takashicompany/palmslave/images/01.jpg

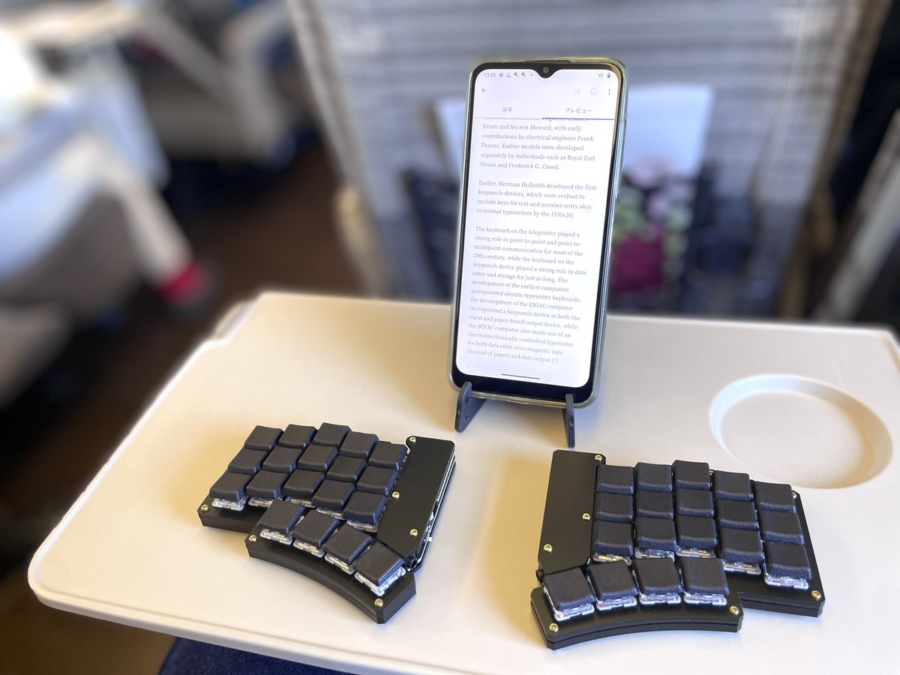
images/01.jpg
