takashicompany/palmslave/images/02.jpg

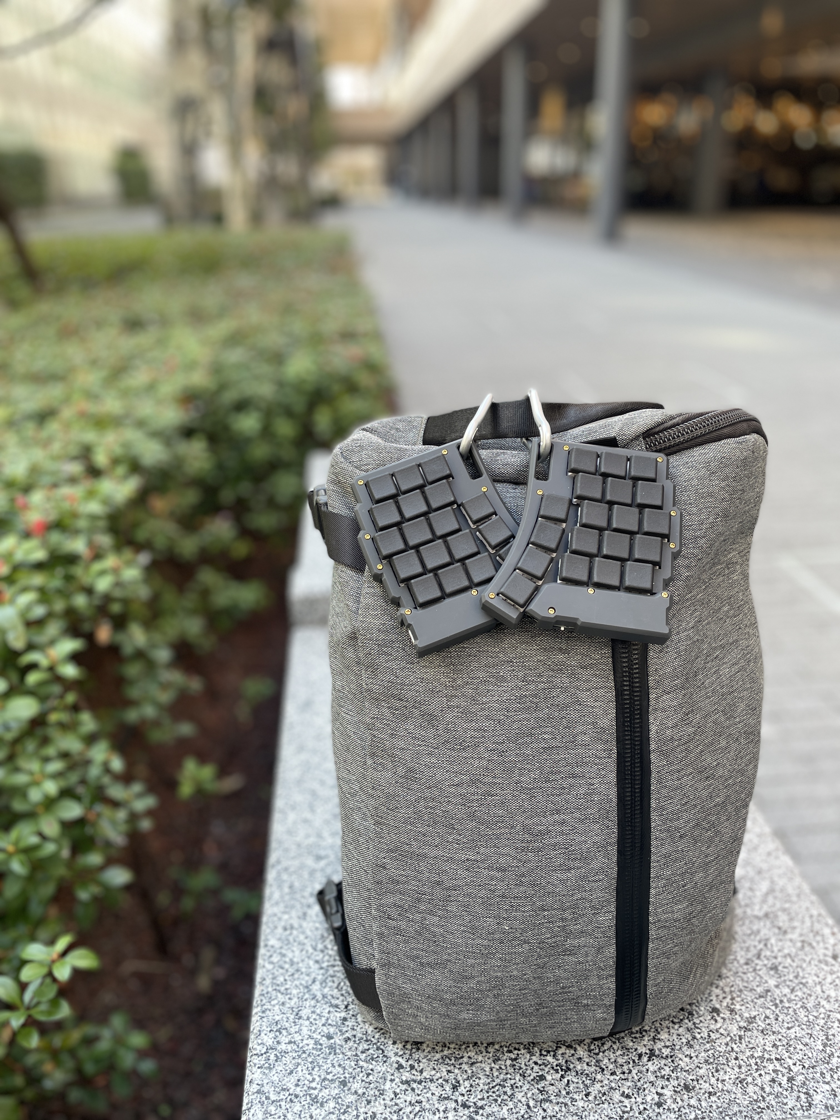
images/02.jpg
