takashicompany/palmslave/images/03.jpg

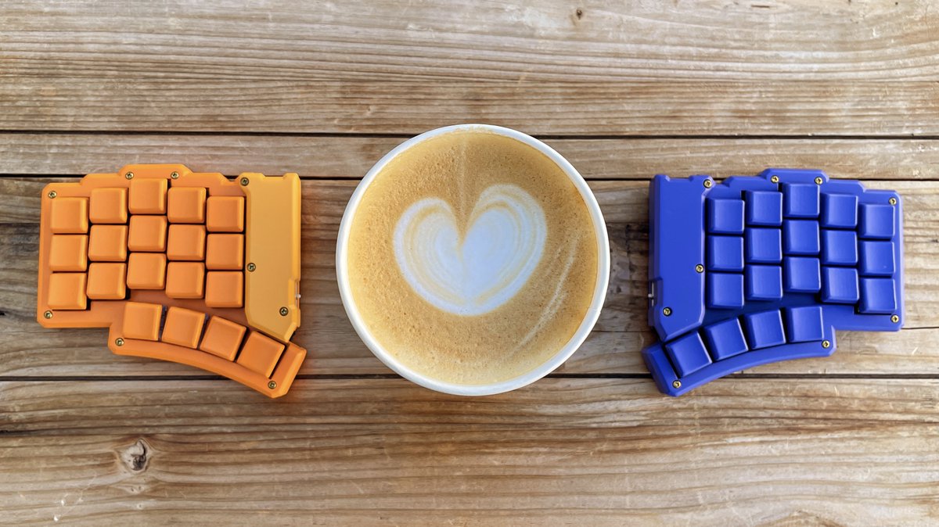
images/03.jpg
