takashicompany/palmslave/images/05.jpg

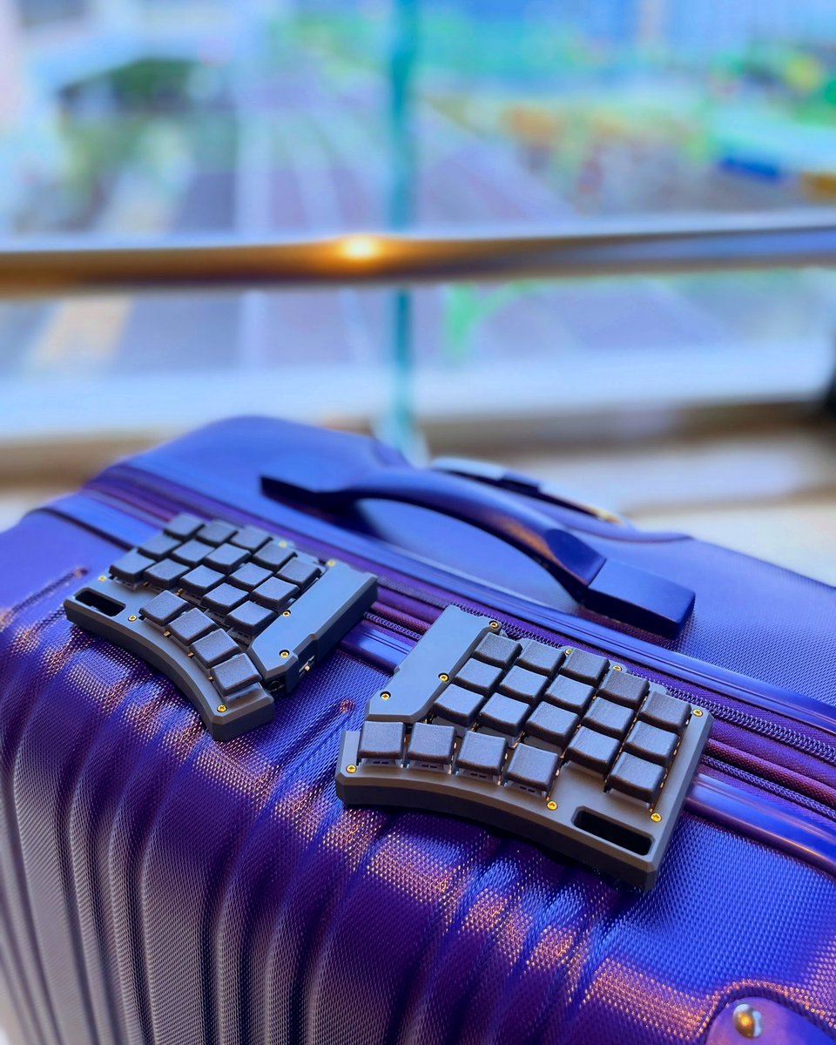
images/05.jpg
