takashicompany/palmslave/images/11.jpg

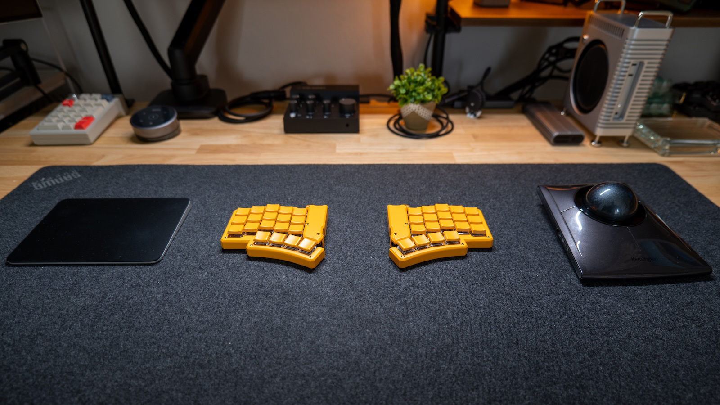
images/11.jpg
