takashicompany/palmslave/images/kawamura/20250201-SDIM0543.jpg

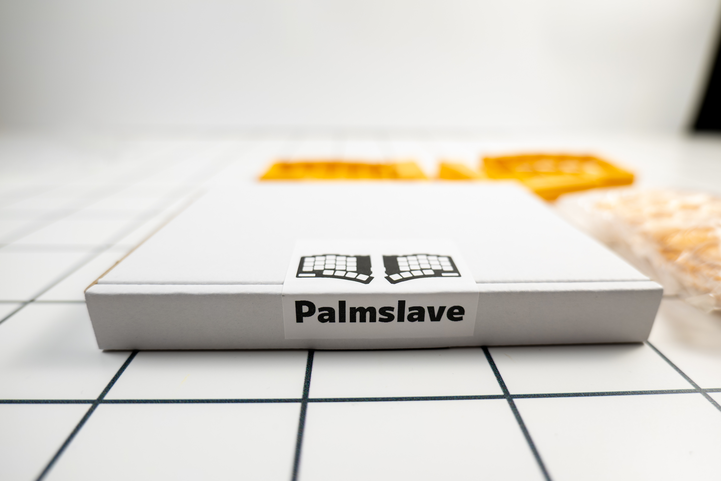
images/kawamura/20250201-SDIM0543.jpg
