takashicompany/palmslave/images/kawamura/20250201-SDIM0548.jpg

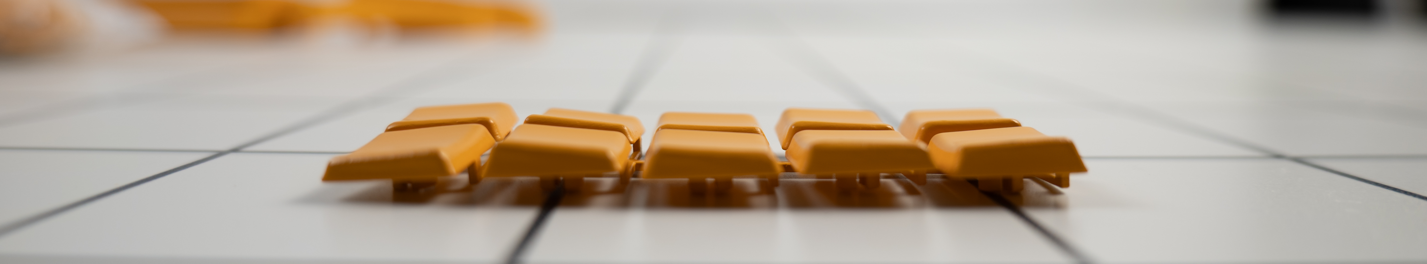
images/kawamura/20250201-SDIM0548.jpg
