takashicompany/palmslave/images/kawamura/20250203-SDIM0584.jpg

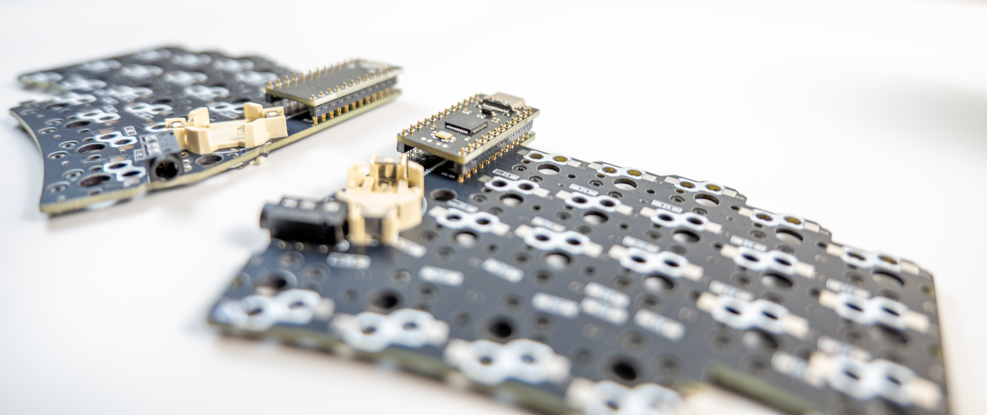
images/kawamura/20250203-SDIM0584.jpg
