takashicompany/palmslave/images/kawamura/20250203-SDIM0585.jpg

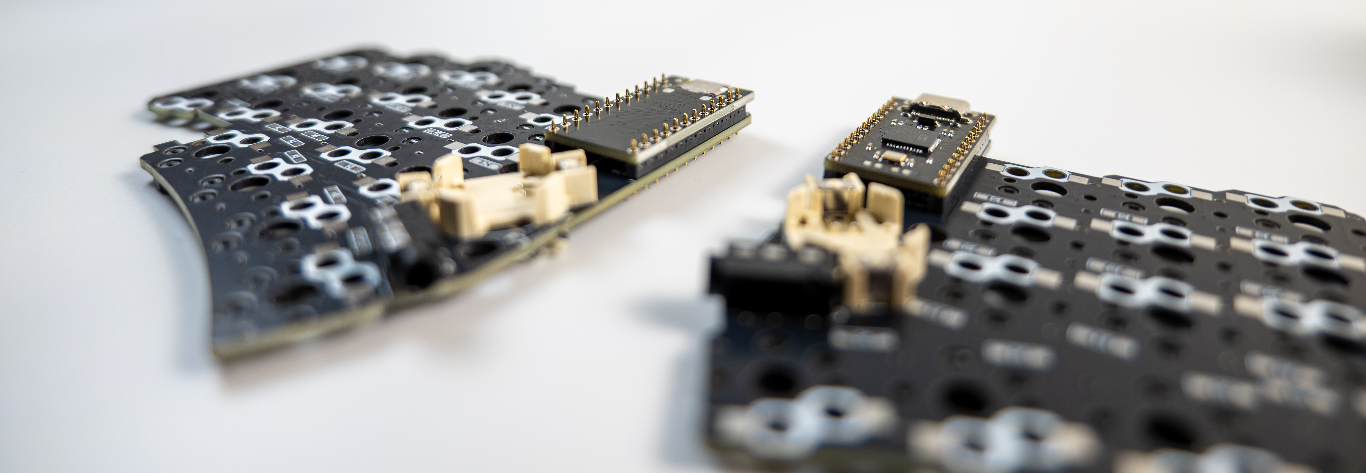
images/kawamura/20250203-SDIM0585.jpg
