takashicompany/palmslave/images/kawamura/20250203-SDIM0596.jpg

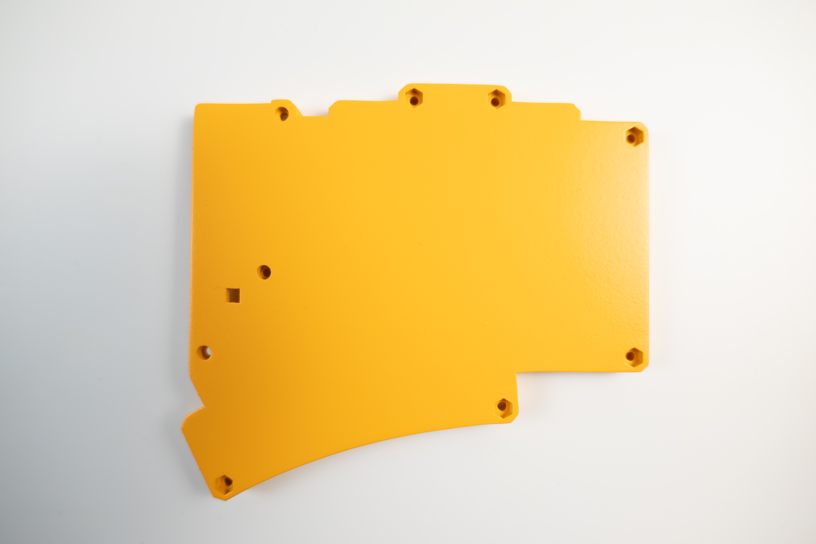
images/kawamura/20250203-SDIM0596.jpg
