takashicompany/palmslave/images/kawamura/20250203-SDIM0607.jpg

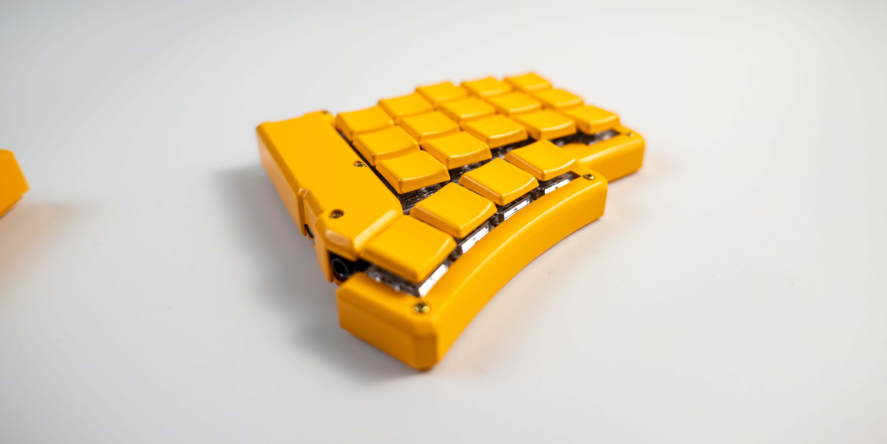
images/kawamura/20250203-SDIM0607.jpg
