takashicompany/palmslave/images/kinotsuyo/palmslave-01.jpg

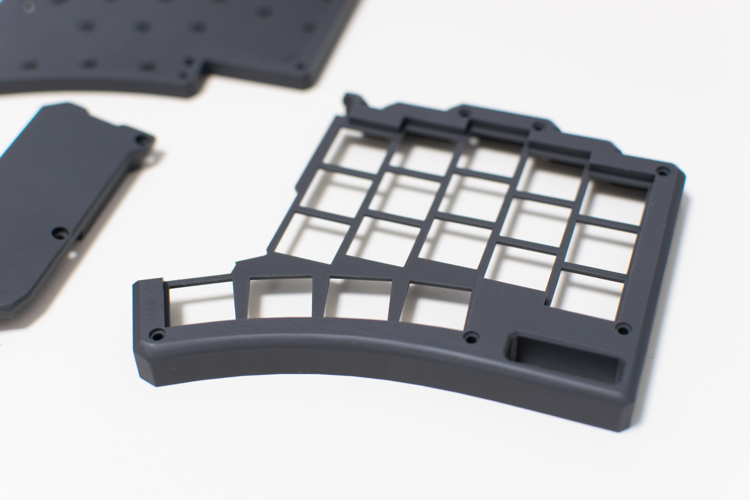
images/kinotsuyo/palmslave-01.jpg
