takashicompany/palmslave/images/kinotsuyo/palmslave-02.jpg

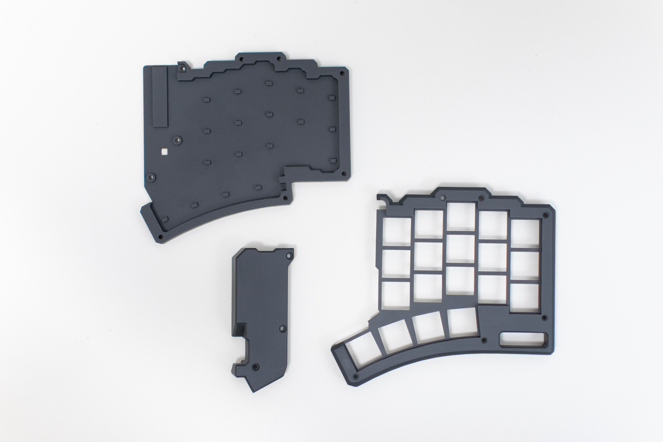
images/kinotsuyo/palmslave-02.jpg
