takashicompany/palmslave/images/kinotsuyo/palmslave-03.jpg

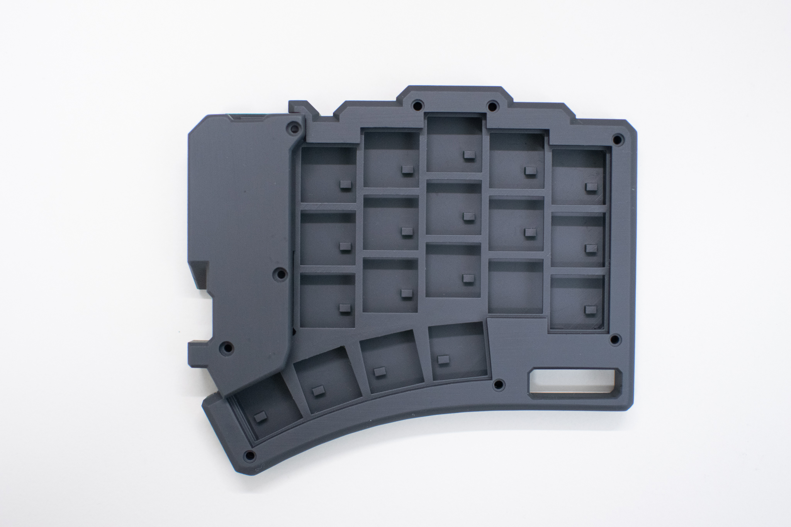
images/kinotsuyo/palmslave-03.jpg
