takashicompany/palmslave/images/kinotsuyo/palmslave-04.jpg

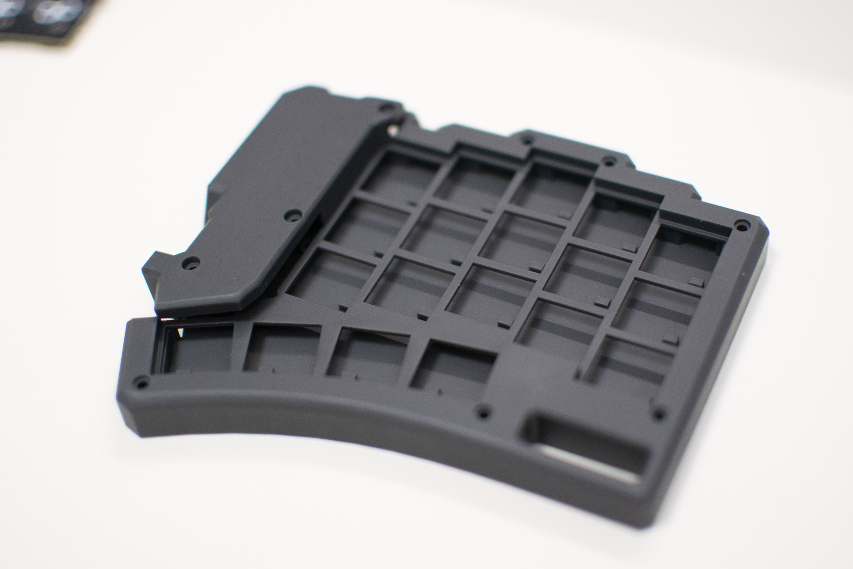
images/kinotsuyo/palmslave-04.jpg
