takashicompany/palmslave/images/kinotsuyo/palmslave-05.jpg

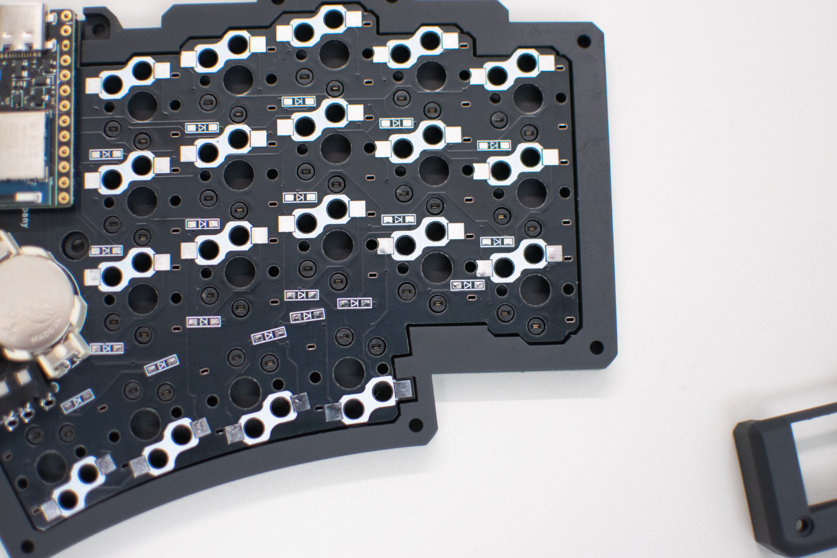
images/kinotsuyo/palmslave-05.jpg
