takashicompany/palmslave/images/kinotsuyo/palmslave-06.jpg

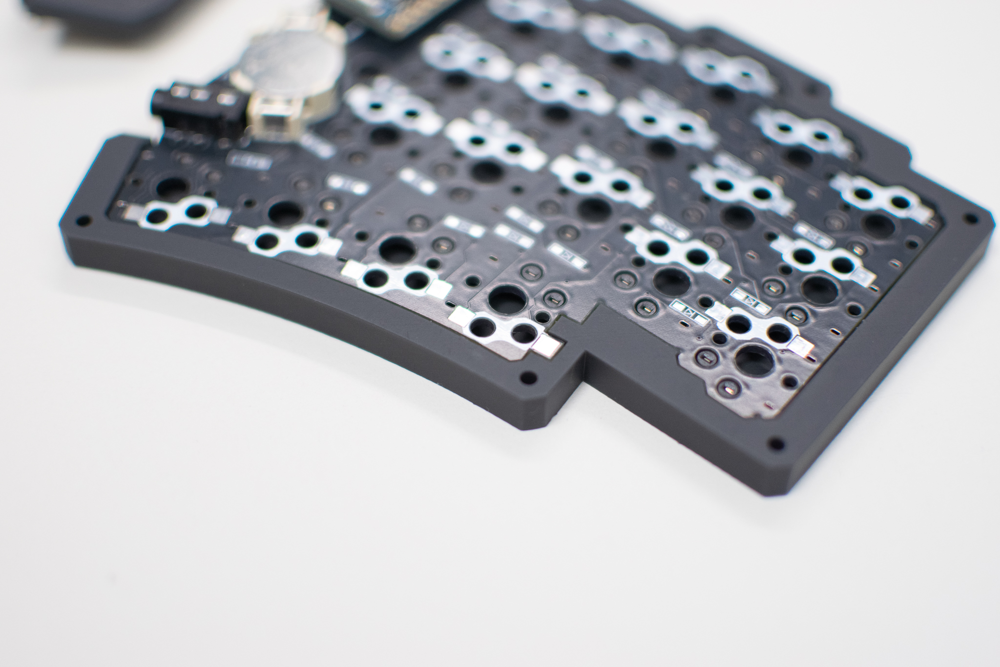
images/kinotsuyo/palmslave-06.jpg
