takashicompany/palmslave/images/kinotsuyo/palmslave-07.jpg

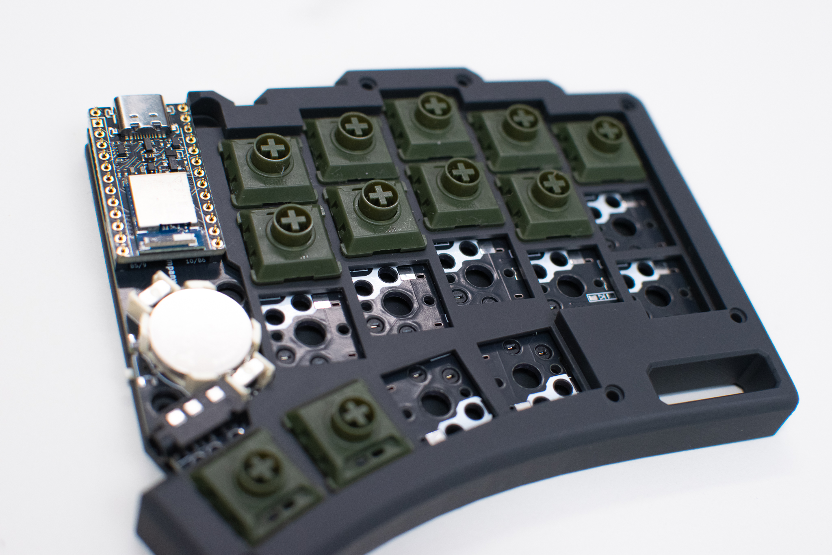
images/kinotsuyo/palmslave-07.jpg
