takashicompany/palmslave/images/kinotsuyo/palmslave-08.jpg

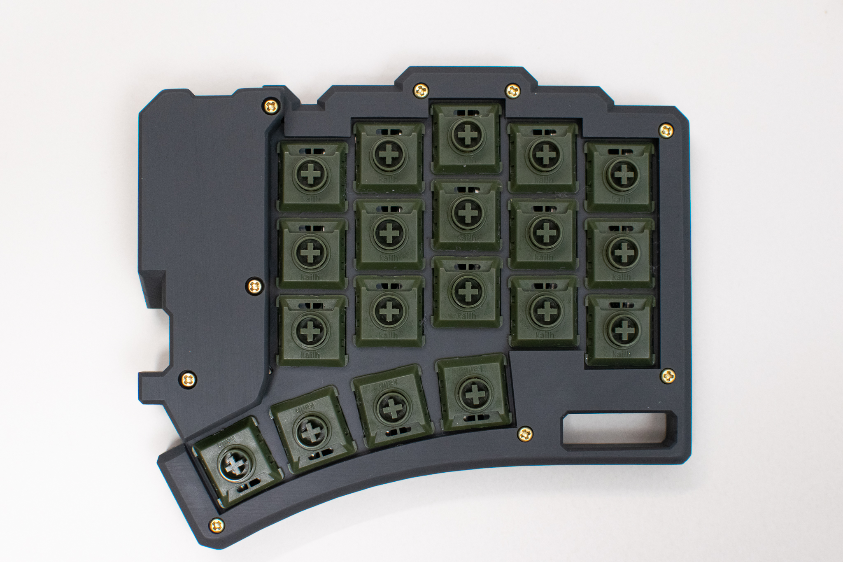
images/kinotsuyo/palmslave-08.jpg
