takashicompany/palmslave/images/kinotsuyo/palmslave-09.jpg

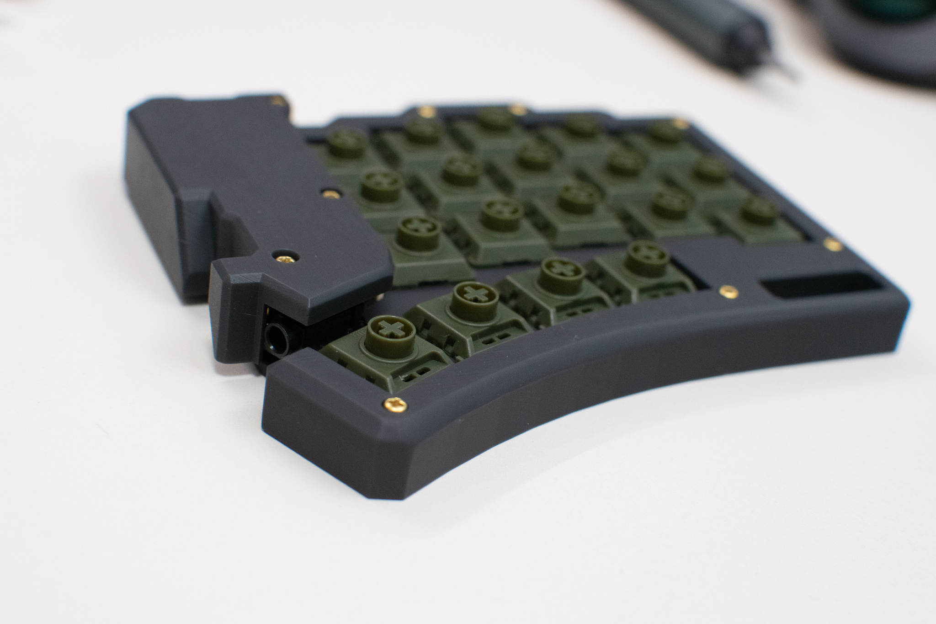
images/kinotsuyo/palmslave-09.jpg
