takashicompany/palmslave/images/kinotsuyo/palmslave-10.jpg

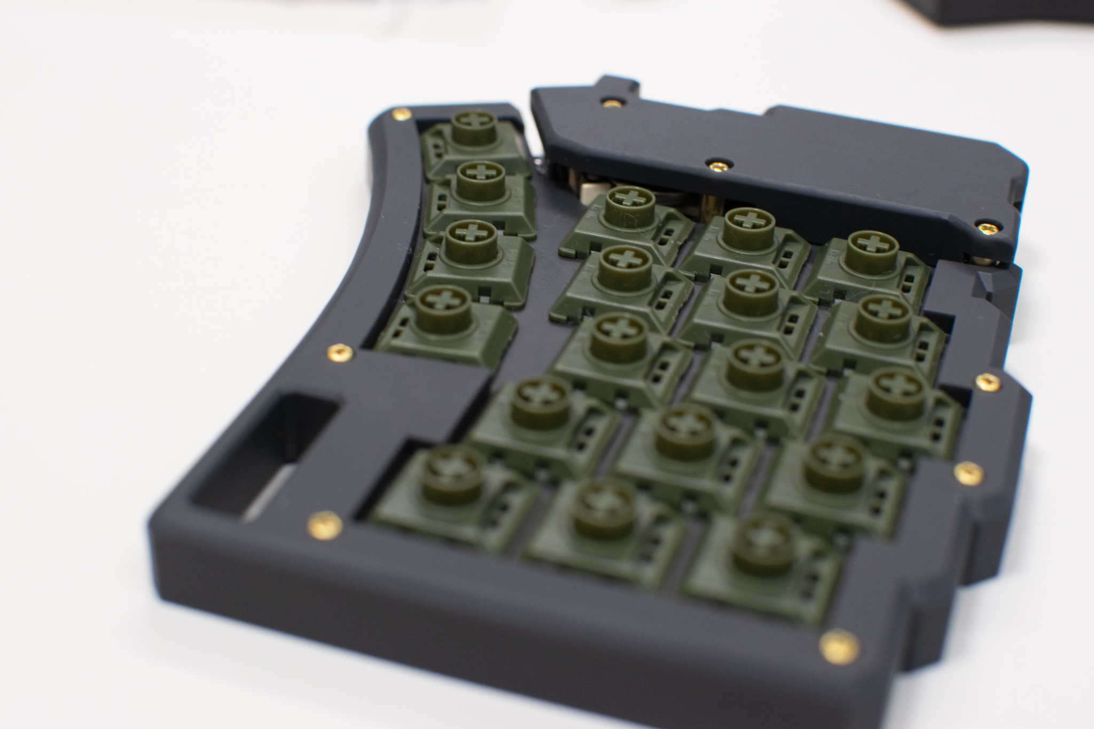
images/kinotsuyo/palmslave-10.jpg
