takashicompany/palmslave/images/kinotsuyo/palmslave-11.jpg

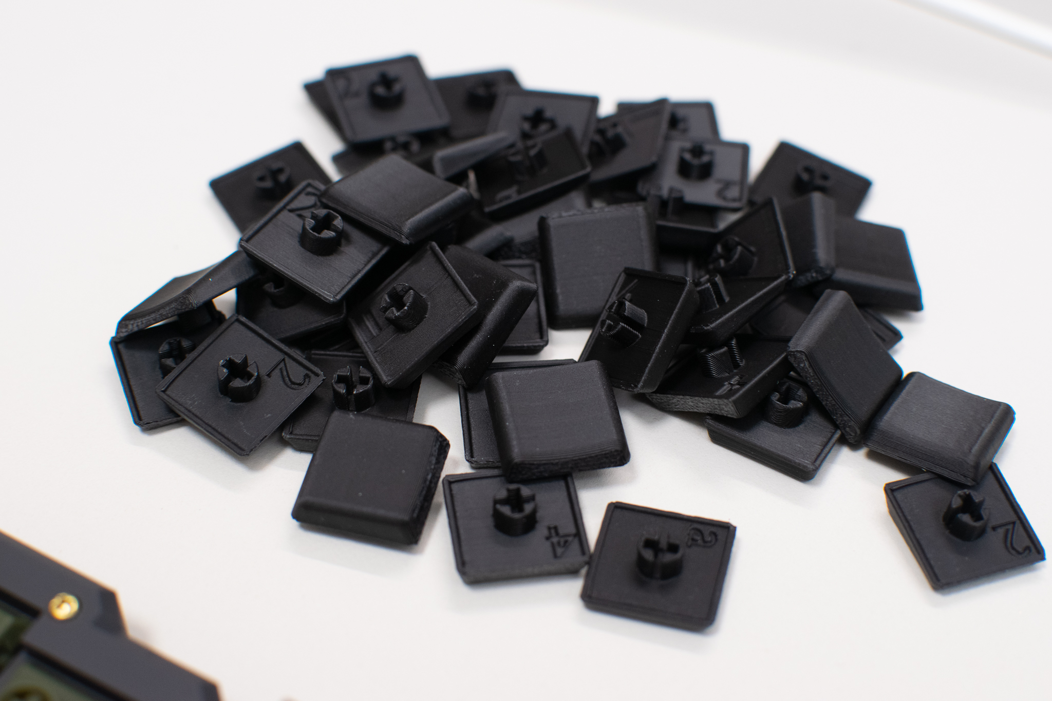
images/kinotsuyo/palmslave-11.jpg
