takashicompany/palmslave/images/kinotsuyo/palmslave-12.jpg

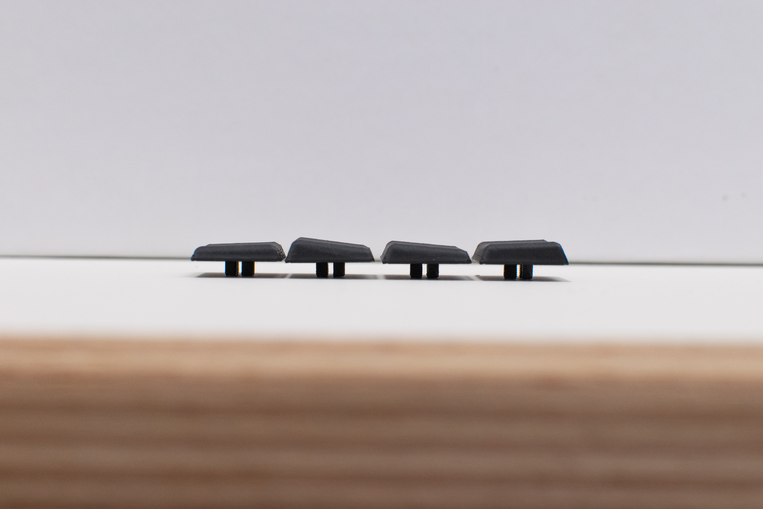
images/kinotsuyo/palmslave-12.jpg
