takashicompany/palmslave/images/kinotsuyo/palmslave-13.jpg

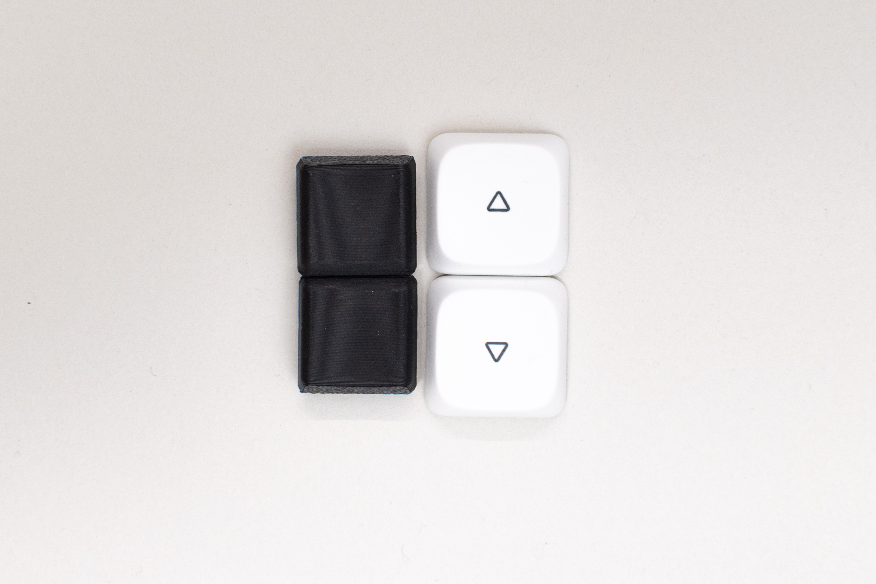
images/kinotsuyo/palmslave-13.jpg
