takashicompany/palmslave/images/kinotsuyo/palmslave-14.jpg

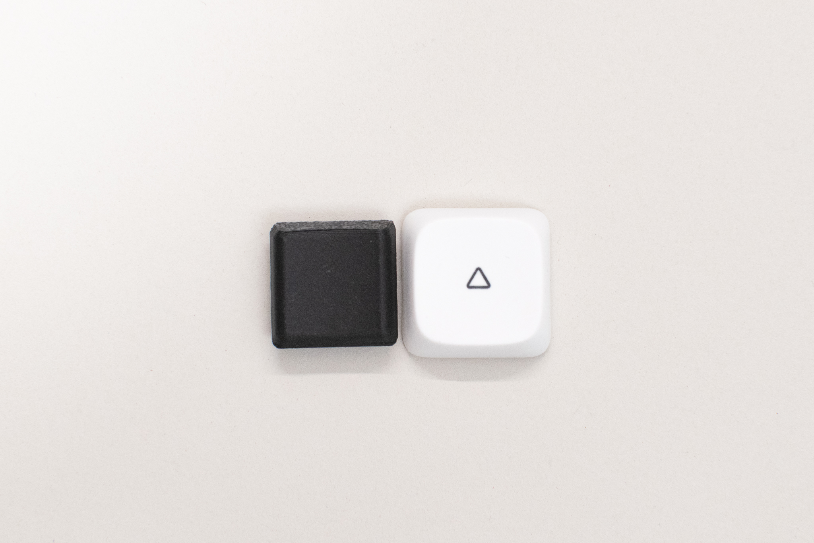
images/kinotsuyo/palmslave-14.jpg
