takashicompany/palmslave/images/kinotsuyo/palmslave-15.jpg

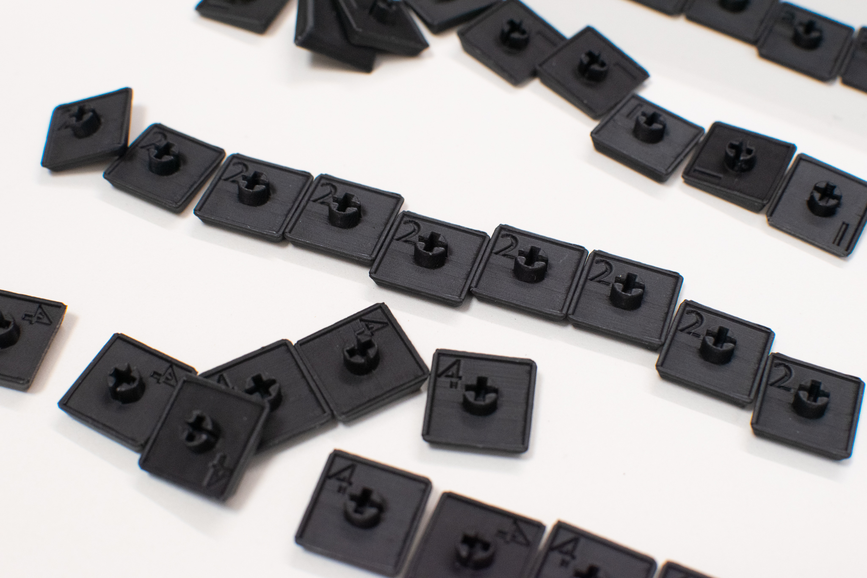
images/kinotsuyo/palmslave-15.jpg
