takashicompany/palmslave/images/kinotsuyo/palmslave-16.jpg

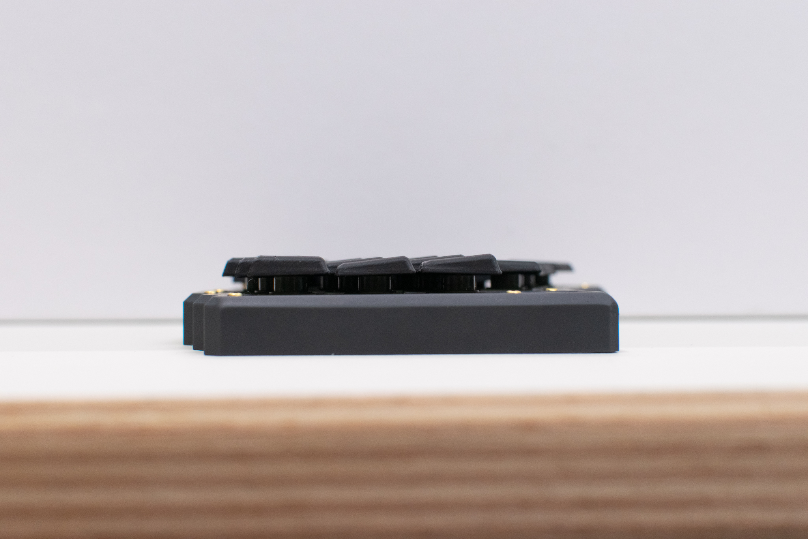
images/kinotsuyo/palmslave-16.jpg
