takashicompany/palmslave/images/kinotsuyo/palmslave-17.jpg

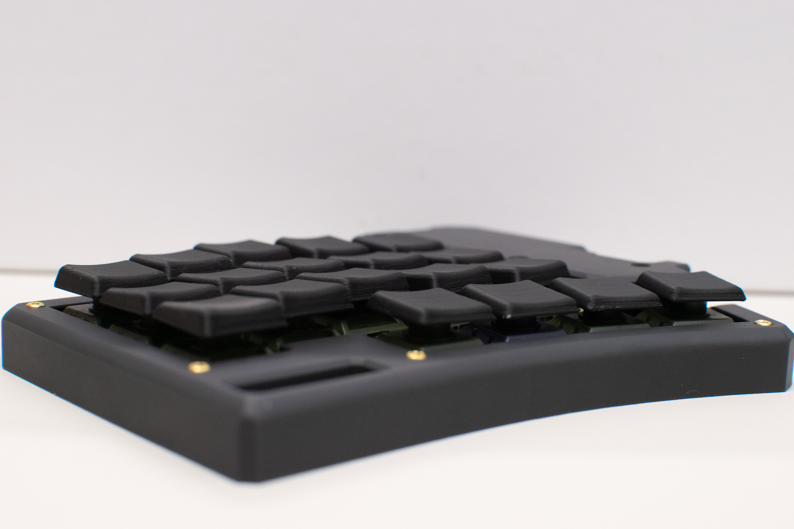
images/kinotsuyo/palmslave-17.jpg
