takashicompany/palmslave/images/kinotsuyo/palmslave-18.jpg

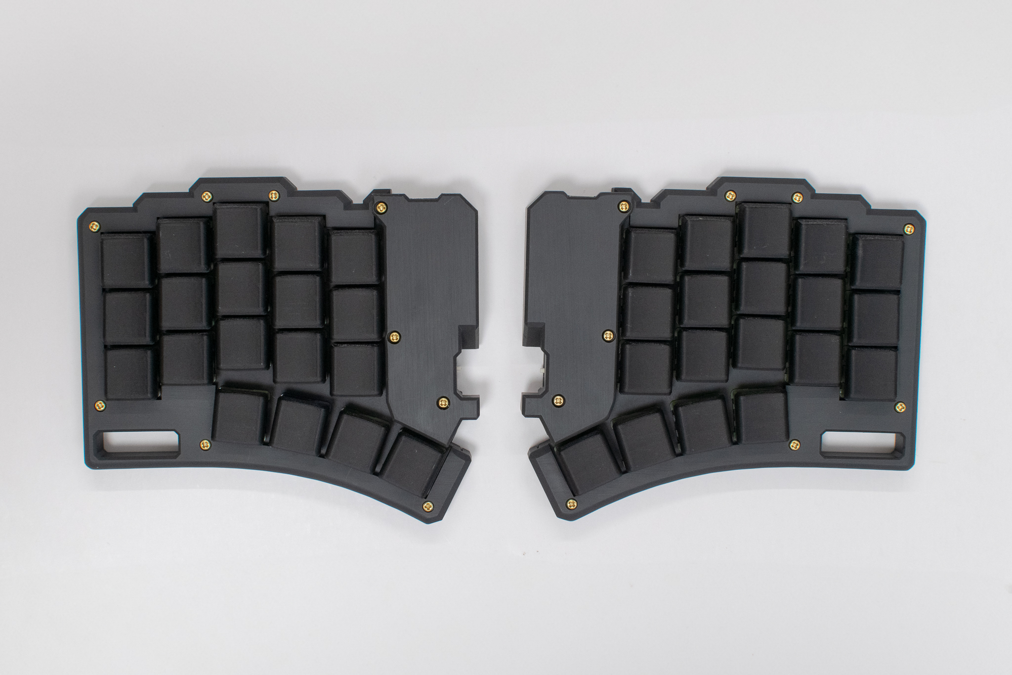
images/kinotsuyo/palmslave-18.jpg
