takashicompany/palmslave/images/kinotsuyo/palmslave-19.jpg

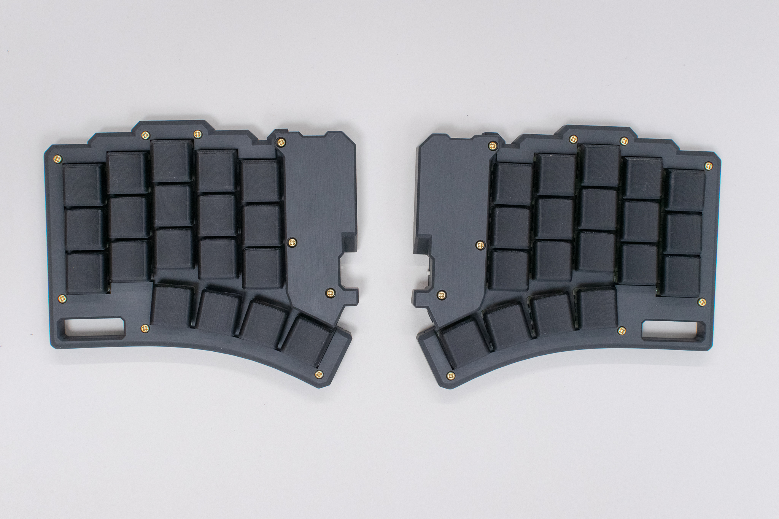
images/kinotsuyo/palmslave-19.jpg
