takashicompany/palmslave/images/kinotsuyo/palmslave-20.jpg

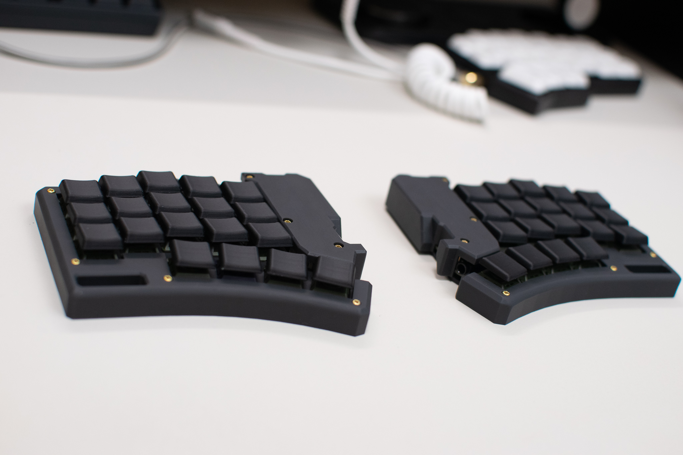
images/kinotsuyo/palmslave-20.jpg
