takashicompany/palmslave/images/kinotsuyo/palmslave-21.jpg

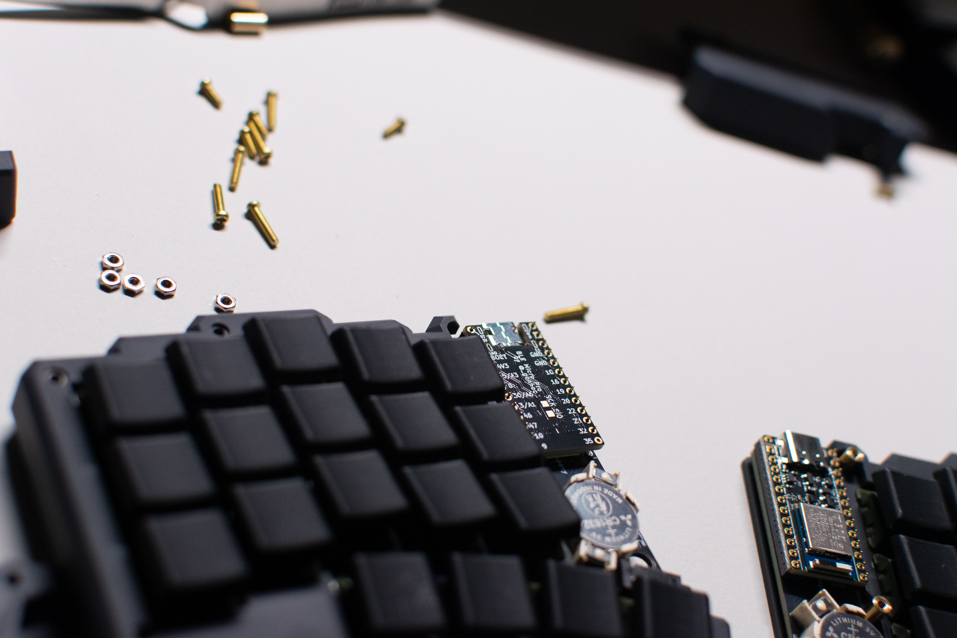
images/kinotsuyo/palmslave-21.jpg
