takashicompany/palmslave/images/kinotsuyo/palmslave-22.jpg

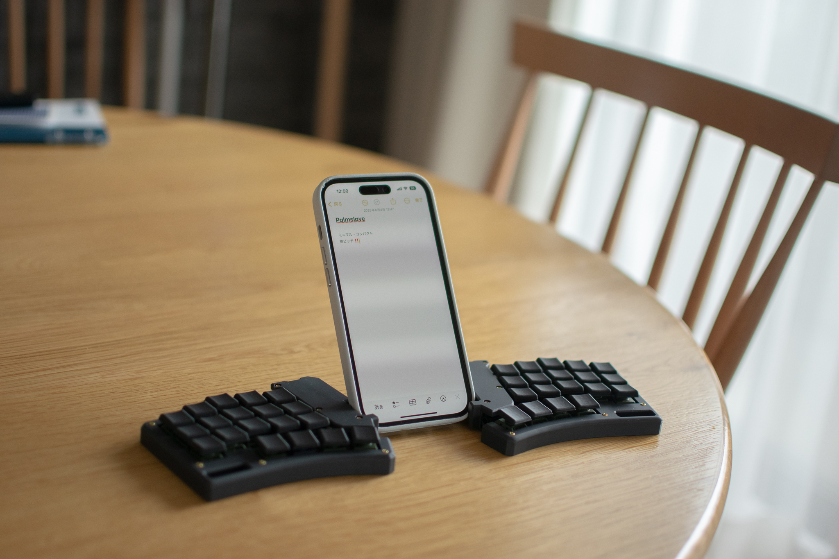
images/kinotsuyo/palmslave-22.jpg
