takashicompany/palmslave/images/kinotsuyo/palmslave-23.jpg

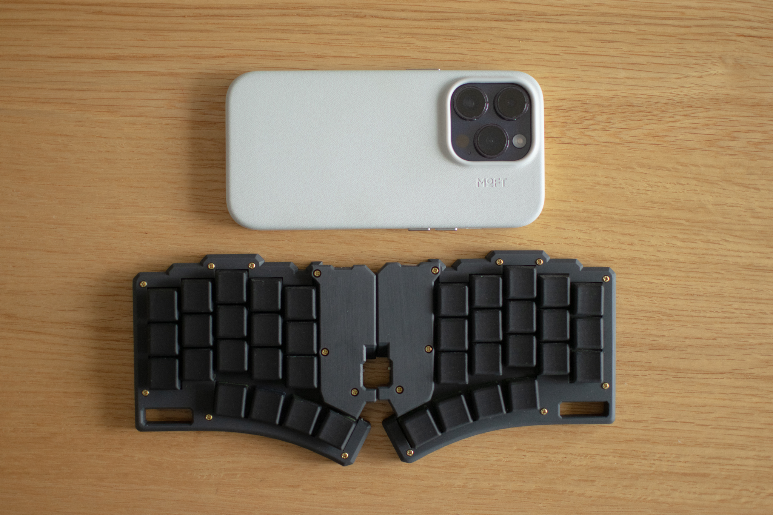
images/kinotsuyo/palmslave-23.jpg
