takashicompany/palmslave/images/kinotsuyo/palmslave-24.jpg

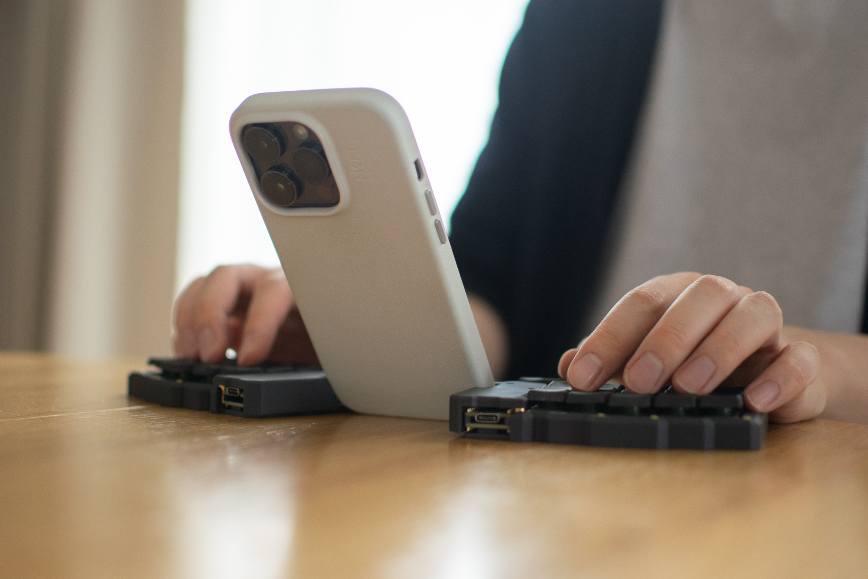
images/kinotsuyo/palmslave-24.jpg
