takashicompany/palmslave/images/kinotsuyo/palmslave-25.jpg

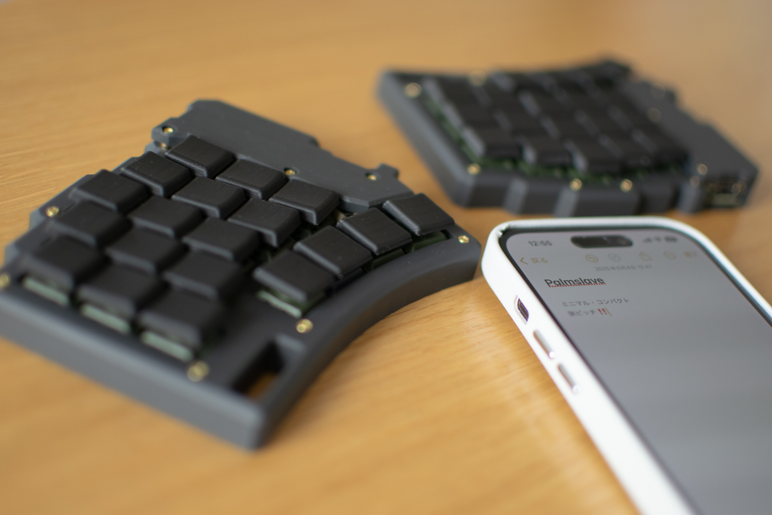
images/kinotsuyo/palmslave-25.jpg
