takashicompany/palmslave/images/kinotsuyo/palmslave-26.jpg

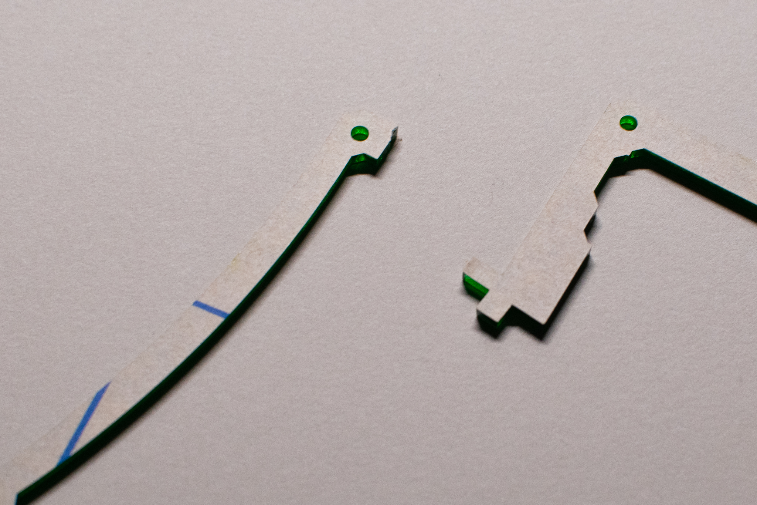
images/kinotsuyo/palmslave-26.jpg
