takashicompany/palmslave/images/kinotsuyo/palmslave-27.jpg

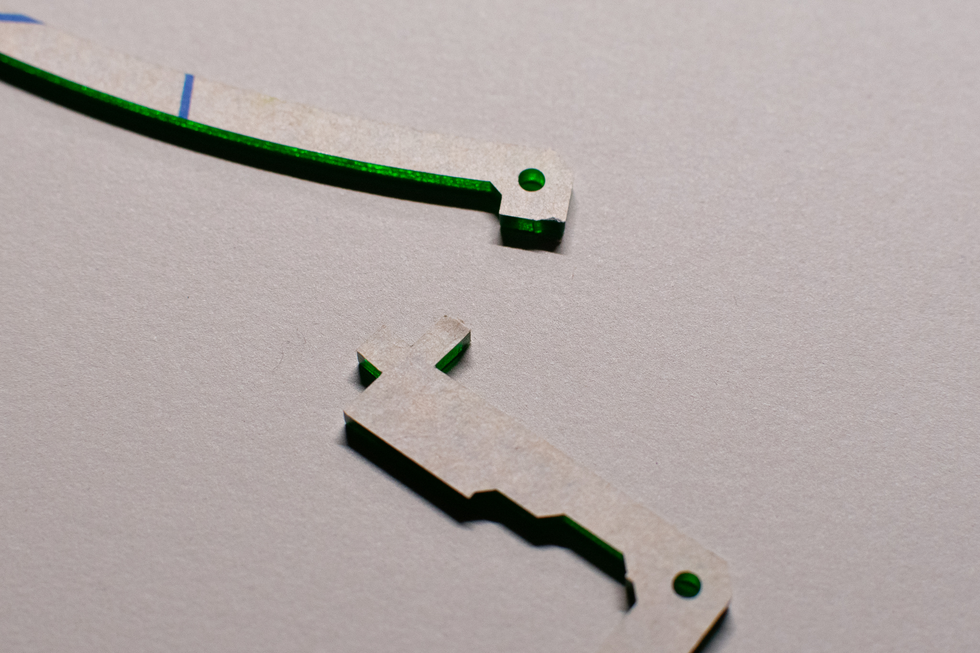
images/kinotsuyo/palmslave-27.jpg
