takashicompany/palmslave/images/kinotsuyo/palmslave-28.jpg

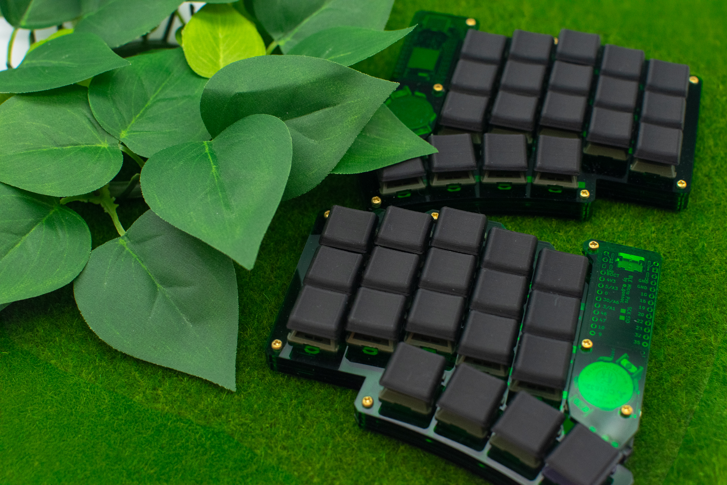
images/kinotsuyo/palmslave-28.jpg
