takashicompany/palmslave/images/kinotsuyo/palmslave-29.jpg

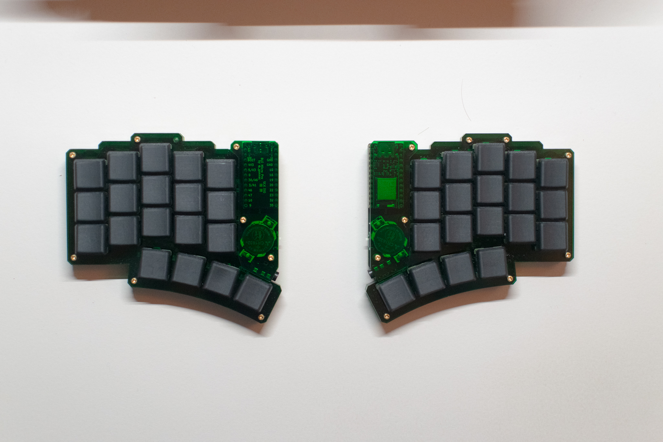
images/kinotsuyo/palmslave-29.jpg
