takashicompany/palmslave/images/kinotsuyo/palmslave-30.jpg

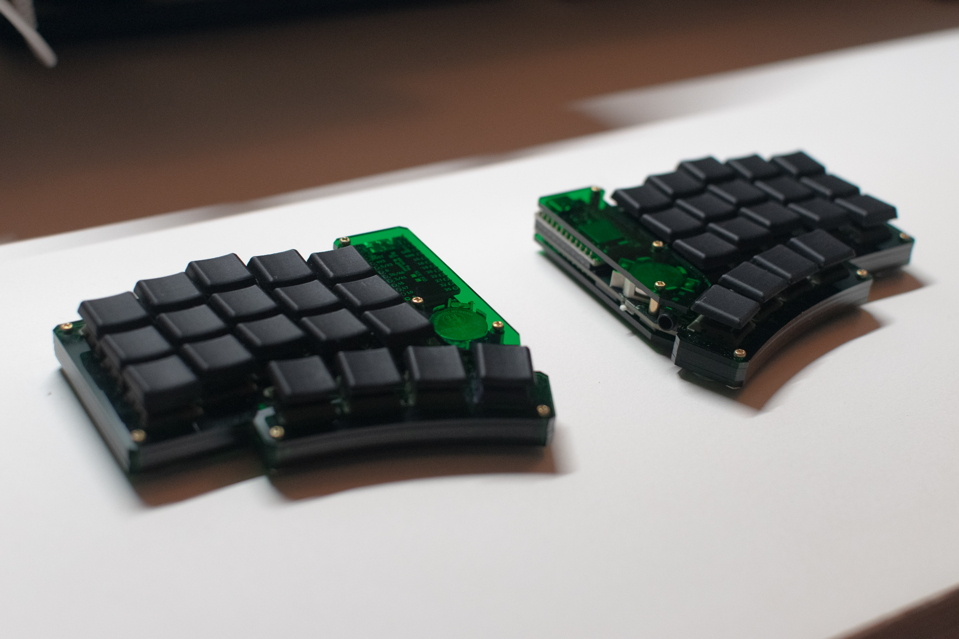
images/kinotsuyo/palmslave-30.jpg
