takashicompany/palmslave/images/kinotsuyo/palmslave-31.jpg

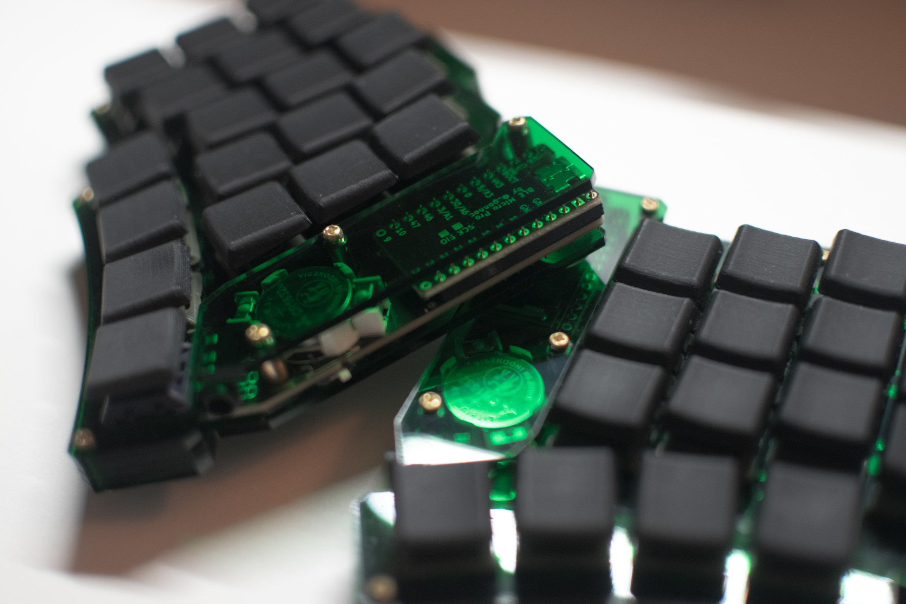
images/kinotsuyo/palmslave-31.jpg
