takashicompany/palmslave/images/kinotsuyo/palmslave-32.jpg

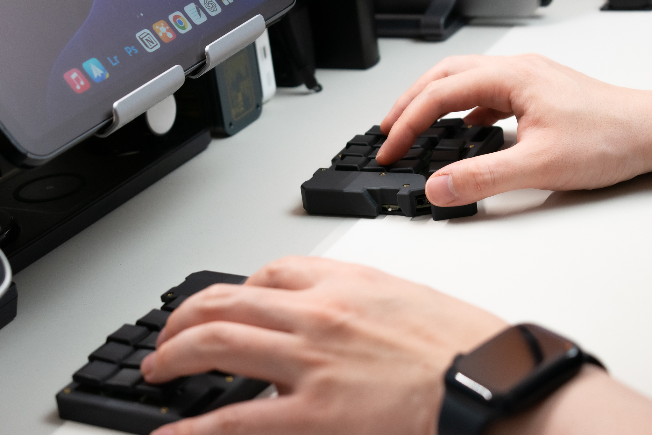
images/kinotsuyo/palmslave-32.jpg
