takashicompany/palmslave/images/kinotsuyo/palmslave-33.jpg

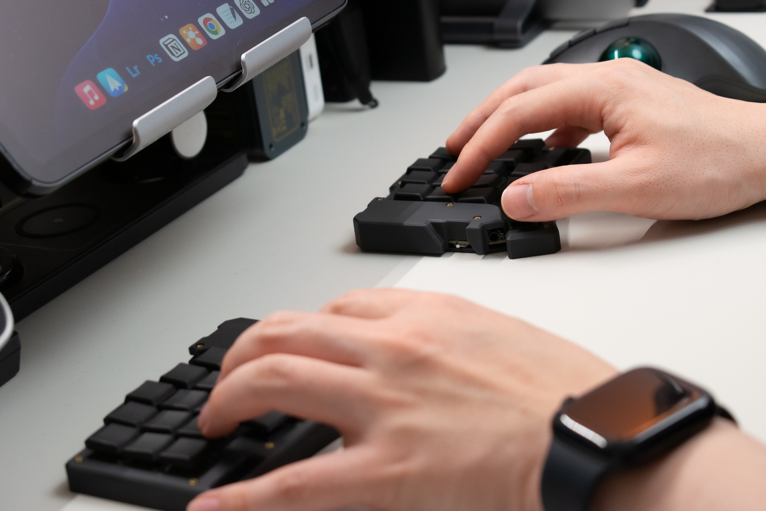
images/kinotsuyo/palmslave-33.jpg
