takashicompany/palmslave/images/kinotsuyo/palmslave-34.jpg

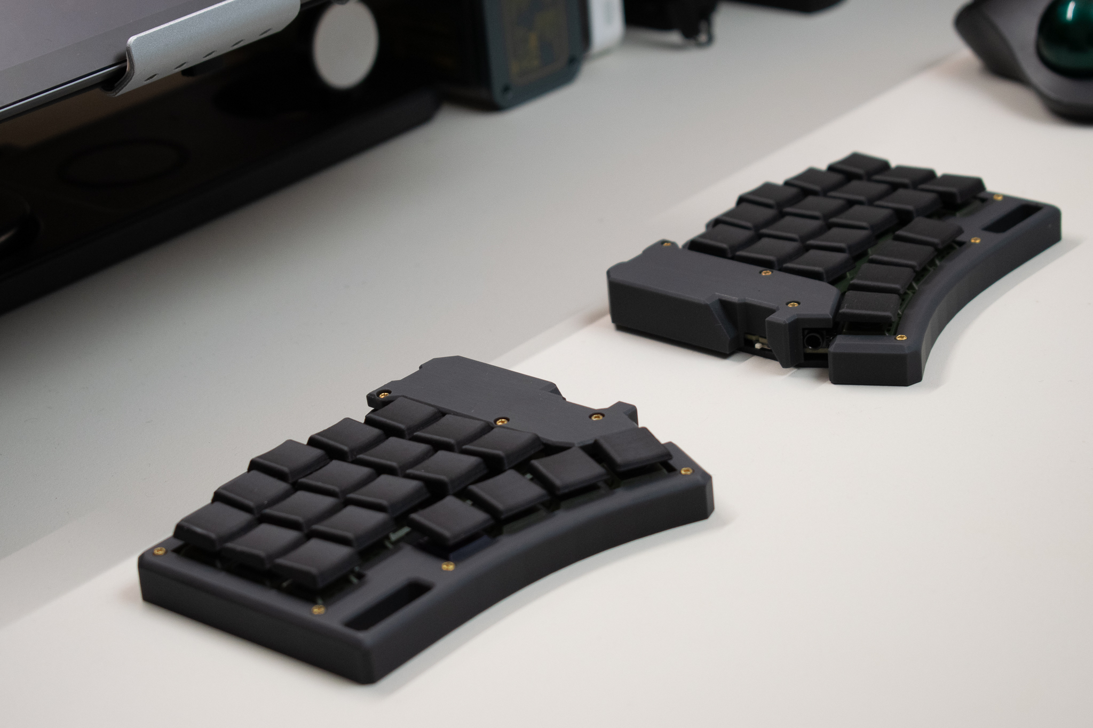
images/kinotsuyo/palmslave-34.jpg
