takashicompany/palmslave/images/kinotsuyo/palmslave-35.jpg

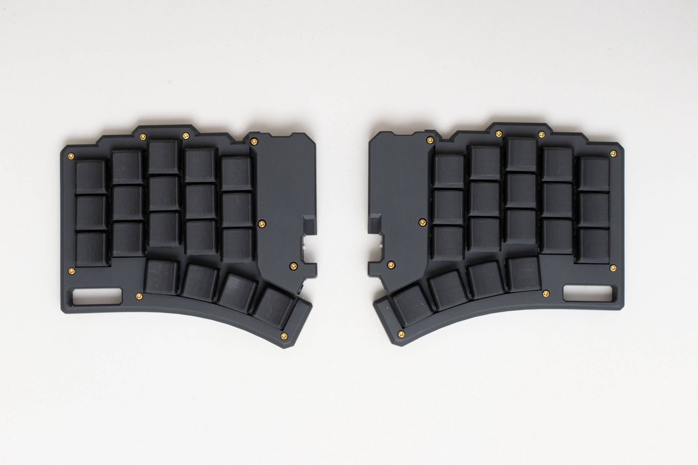
images/kinotsuyo/palmslave-35.jpg
