takashicompany/palmslave/images/kinotsuyo/palmslave-36.jpg

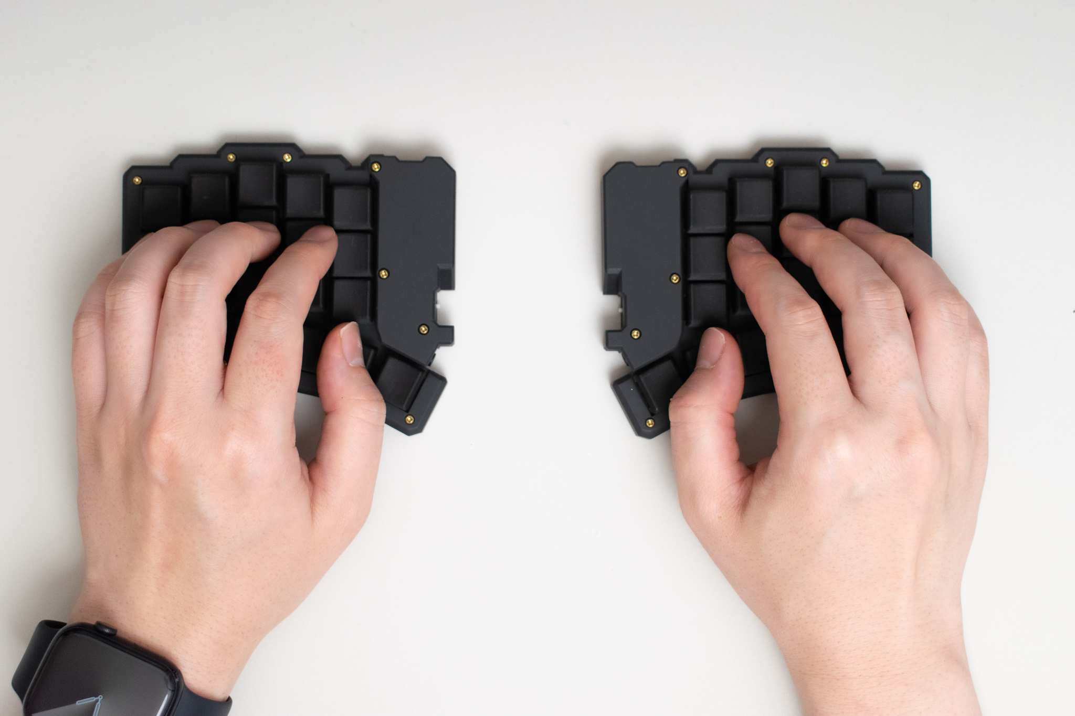
images/kinotsuyo/palmslave-36.jpg
