takashicompany/palmslave/images/kinotsuyo/palmslave-37.jpg

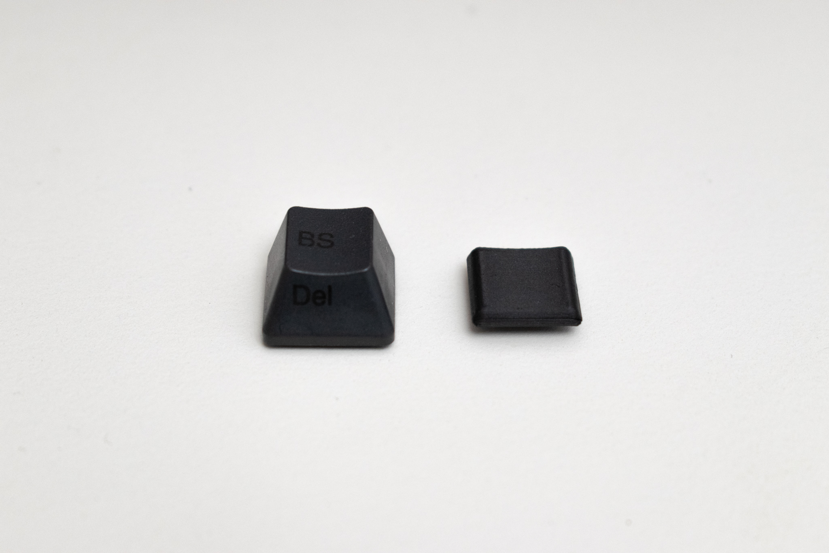
images/kinotsuyo/palmslave-37.jpg
