takashicompany/palmslave/images/kinotsuyo/palmslave-38.jpg

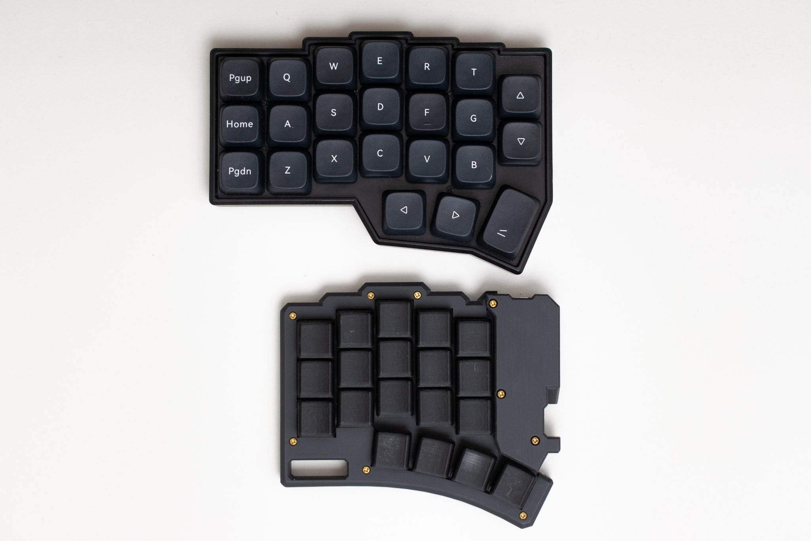
images/kinotsuyo/palmslave-38.jpg
