takashicompany/palmslave/images/kinotsuyo/palmslave-39.jpg

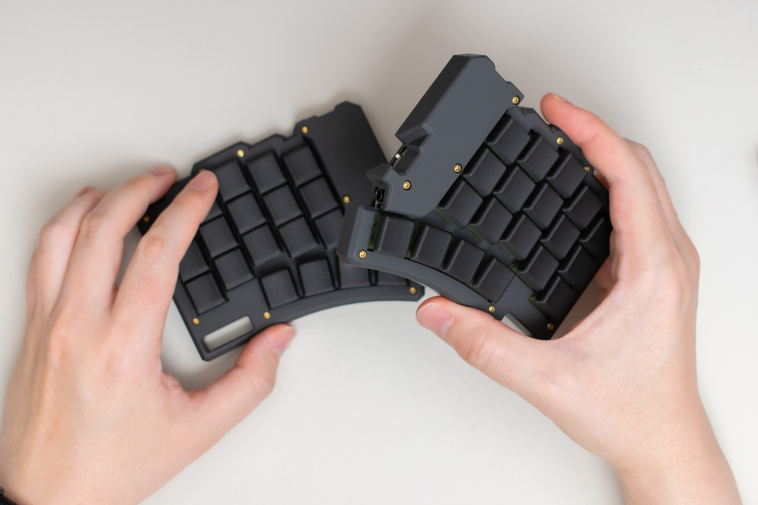
images/kinotsuyo/palmslave-39.jpg
