takashicompany/palmslave/images/kinotsuyo/palmslave-40.jpg

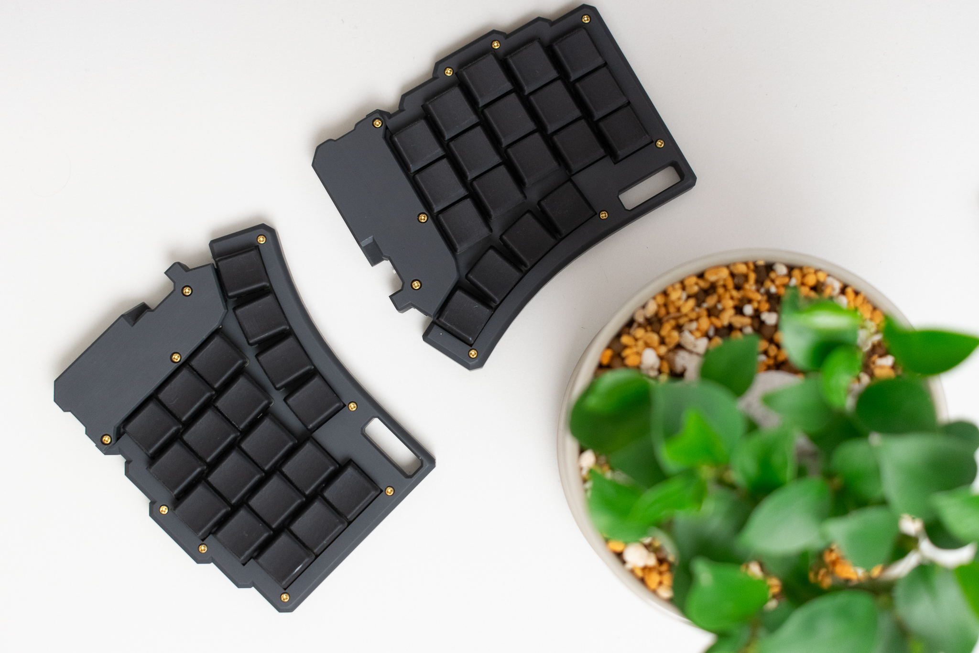
images/kinotsuyo/palmslave-40.jpg
