takashicompany/palmslave/images/kinotsuyo/palmslave-41.jpg

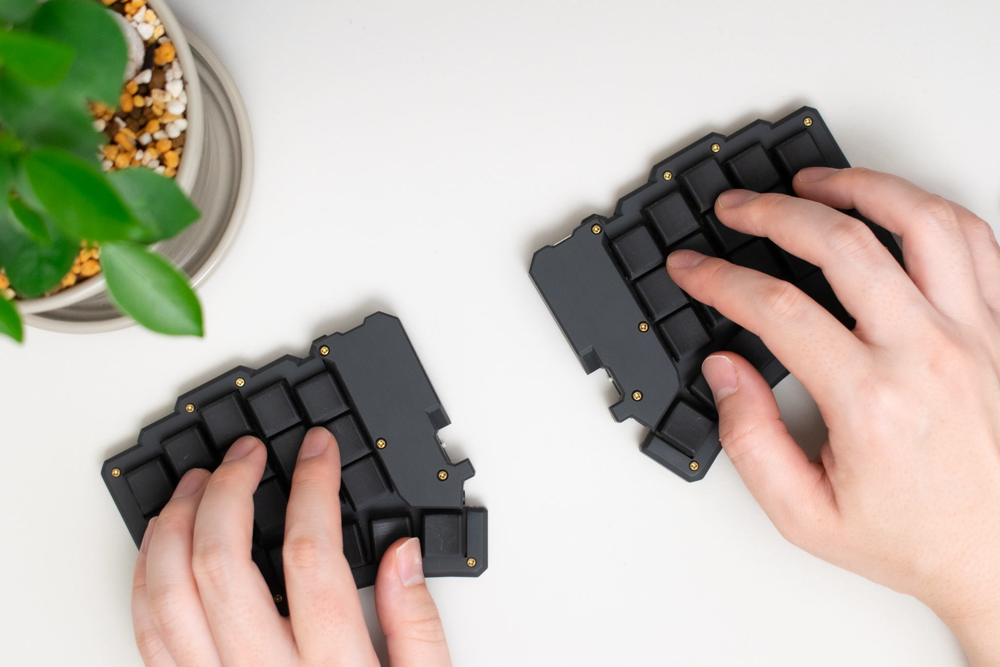
images/kinotsuyo/palmslave-41.jpg
