takashicompany/palmslave/images/kinotsuyo/palmslave-42.jpg

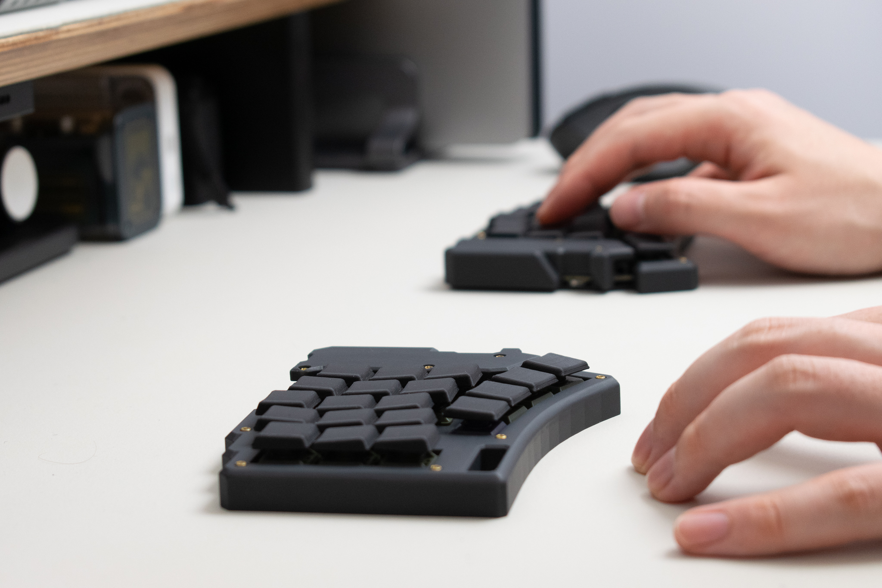
images/kinotsuyo/palmslave-42.jpg
