takashicompany/palmslave/images/kinotsuyo/palmslave-43.jpg

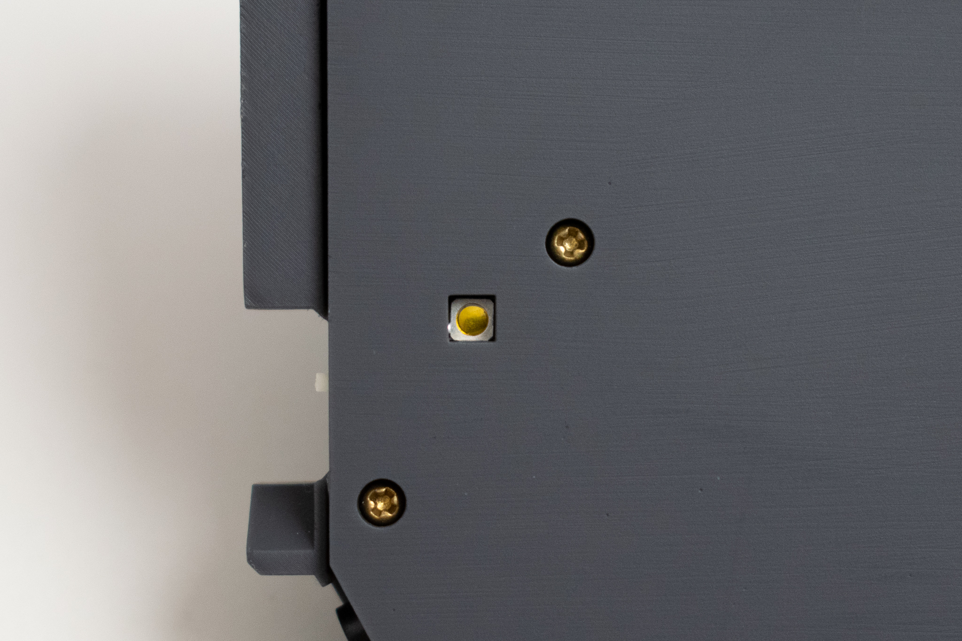
images/kinotsuyo/palmslave-43.jpg
