takashicompany/palmslave/images/kinotsuyo/palmslave-44.jpg

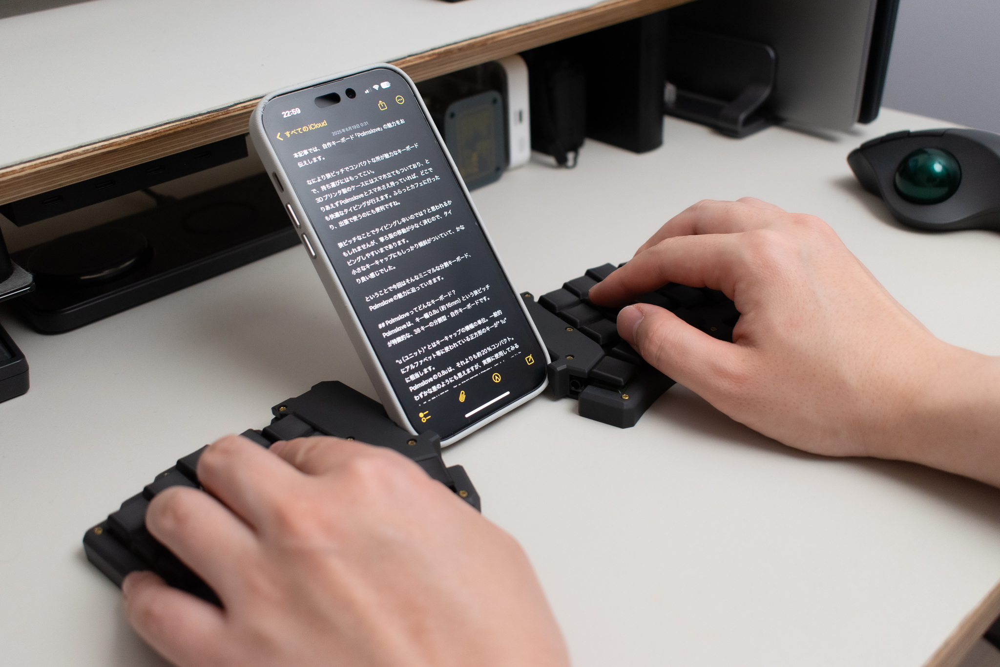
images/kinotsuyo/palmslave-44.jpg
