takashicompany/palmslave/images/kinotsuyo/palmslave-45.jpg

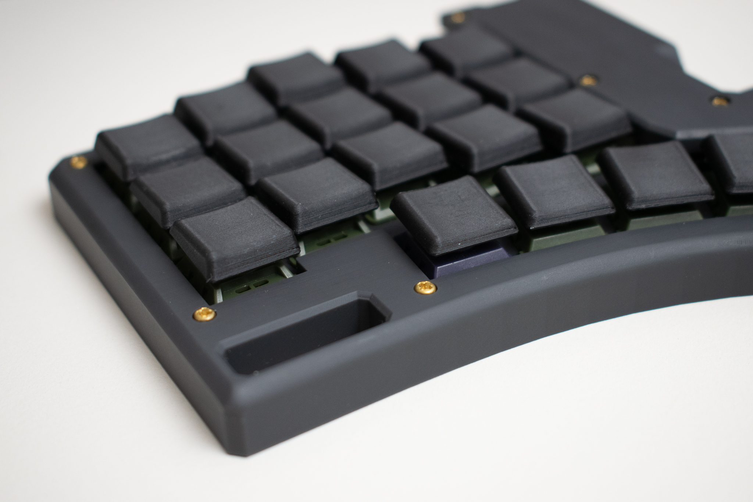
images/kinotsuyo/palmslave-45.jpg
