takashicompany/palmslave/images/kinotsuyo/palmslave-46.jpg

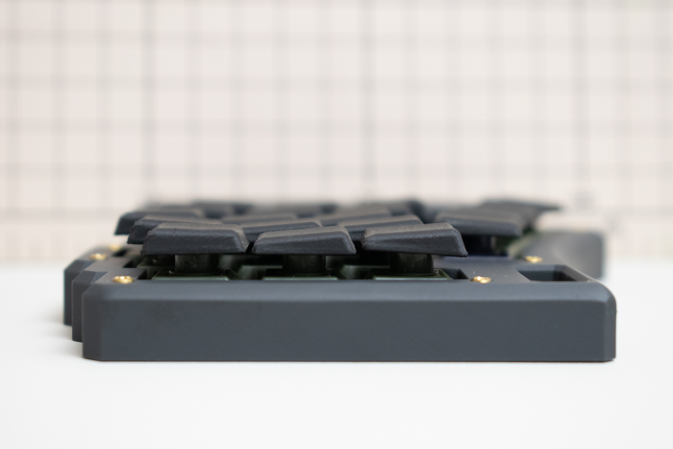
images/kinotsuyo/palmslave-46.jpg
