takashicompany/palmslave/images/kinotsuyo/palmslave-47.jpg

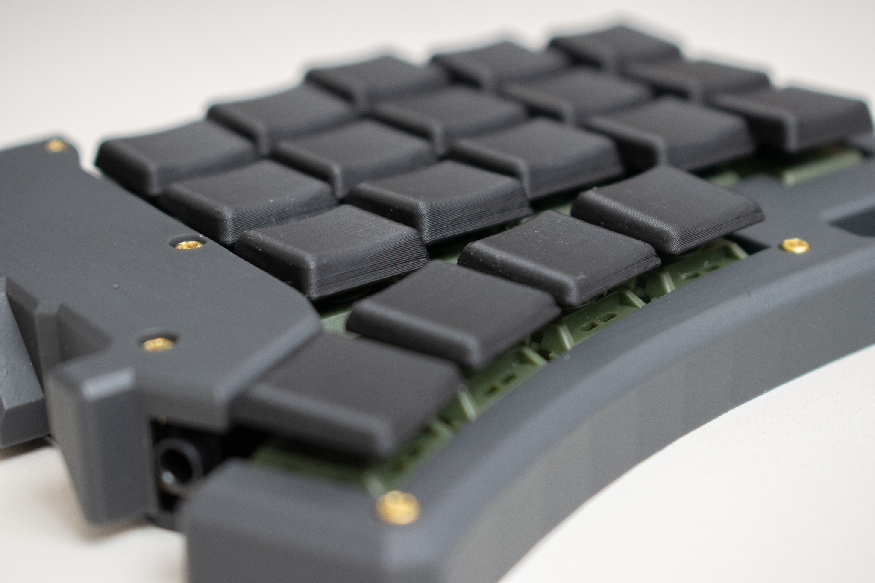
images/kinotsuyo/palmslave-47.jpg
