takashicompany/palmslave/images/kinotsuyo/palmslave-48.jpg

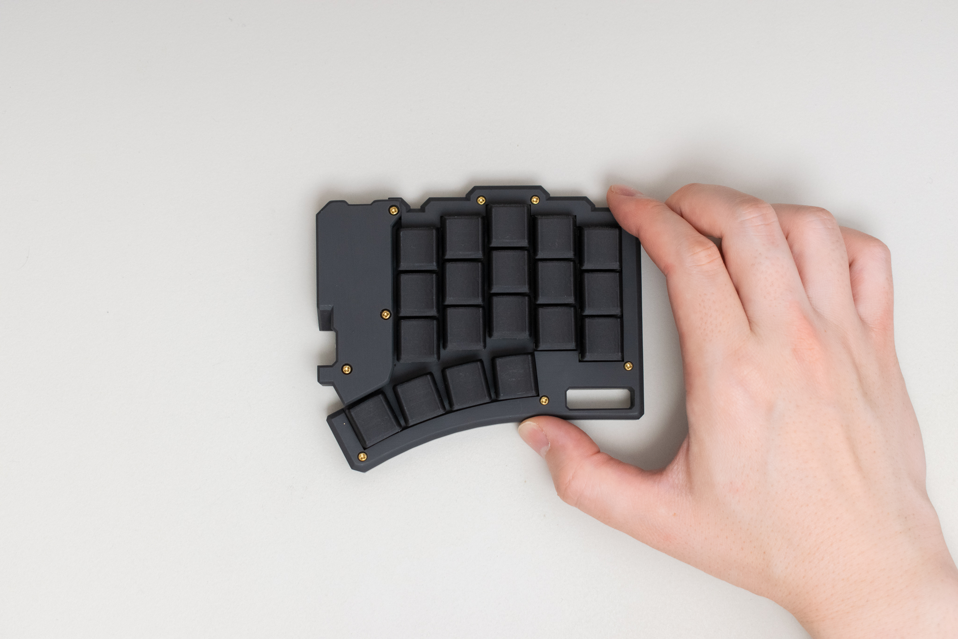
images/kinotsuyo/palmslave-48.jpg
