takashicompany/palmslave/images/kinotsuyo/palmslave-49.jpg

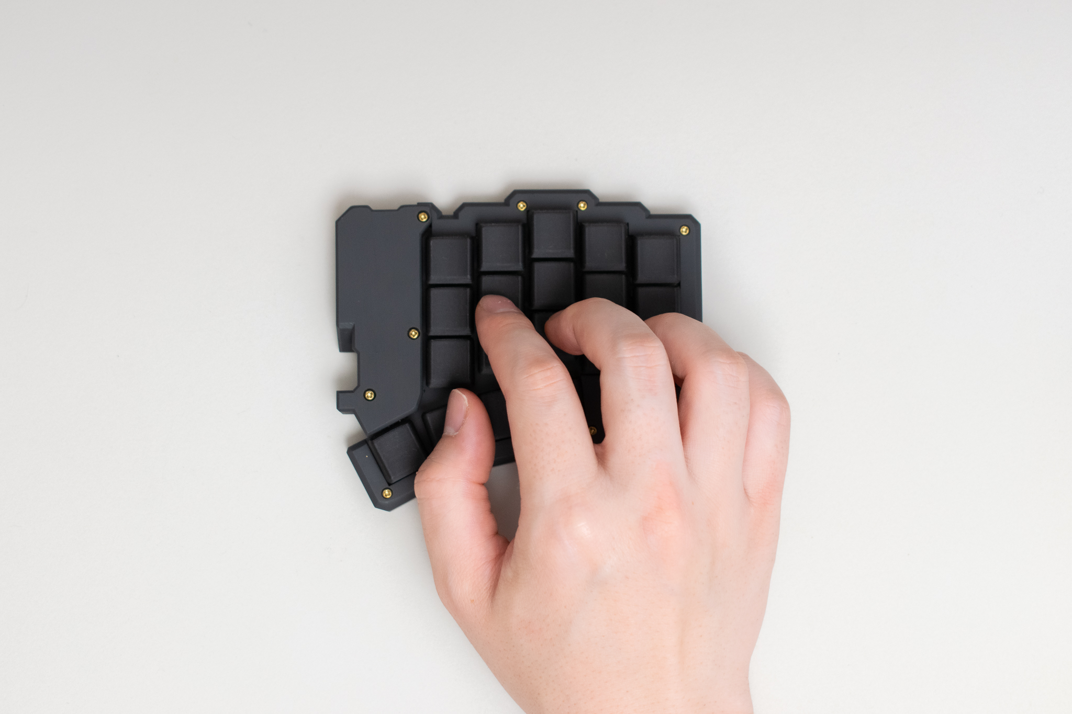
images/kinotsuyo/palmslave-49.jpg
