takashicompany/palmslave/images/kinotsuyo/palmslave-50.jpg

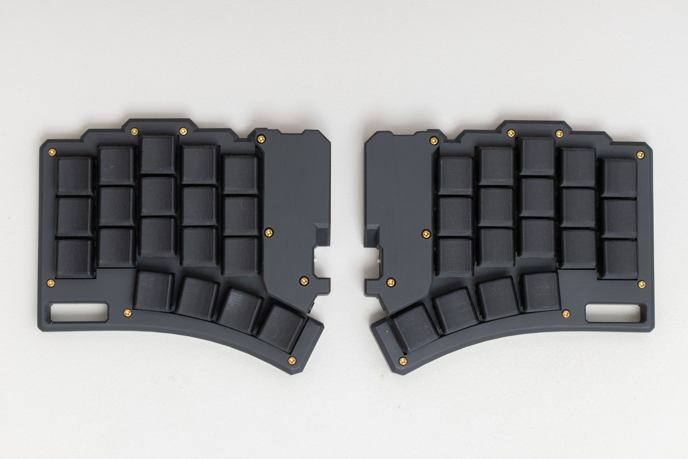
images/kinotsuyo/palmslave-50.jpg
