takashicompany/palmslave/images/kinotsuyo/palmslave-51.jpg

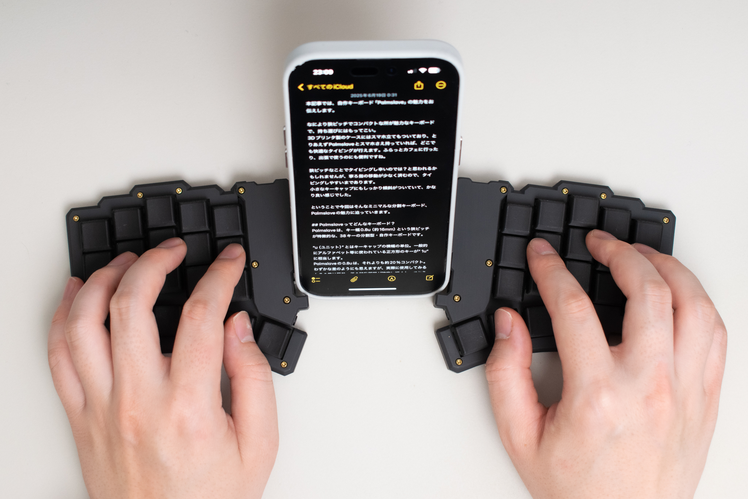
images/kinotsuyo/palmslave-51.jpg
