takashicompany/palmslave/images/kinotsuyo/palmslave-52.jpg

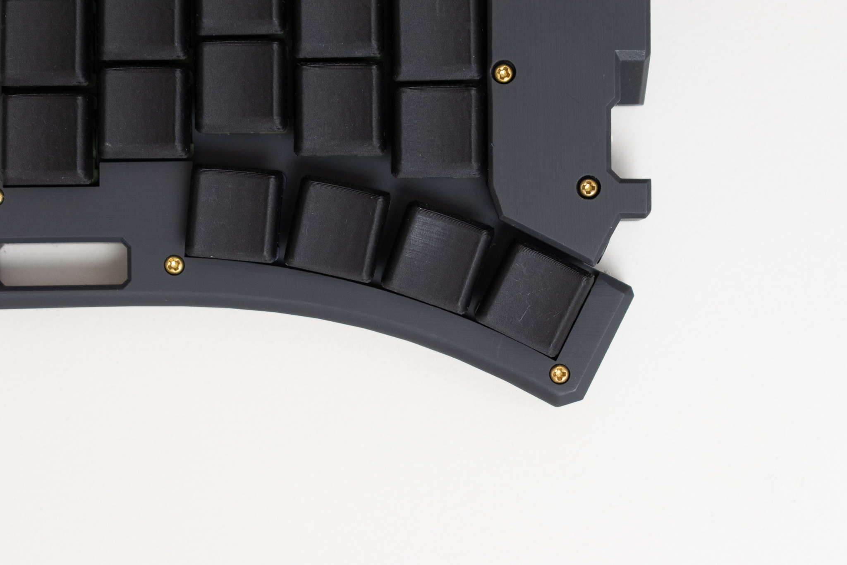
images/kinotsuyo/palmslave-52.jpg
