takashicompany/palmslave/images/kinotsuyo/palmslave-53.jpg

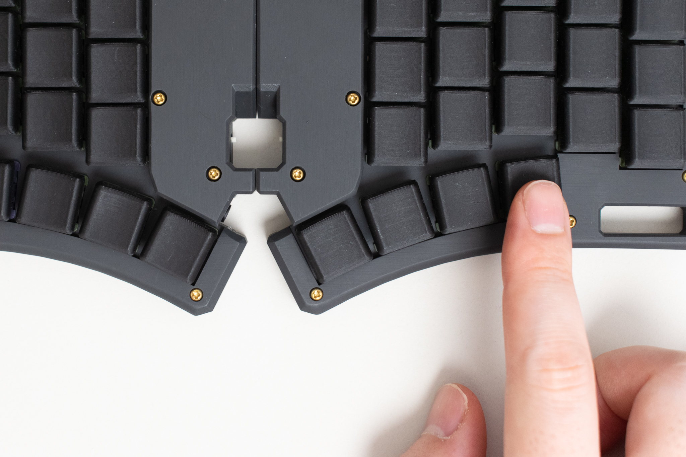
images/kinotsuyo/palmslave-53.jpg
