takashicompany/palmslave/images/kinotsuyo/palmslave-54.jpg

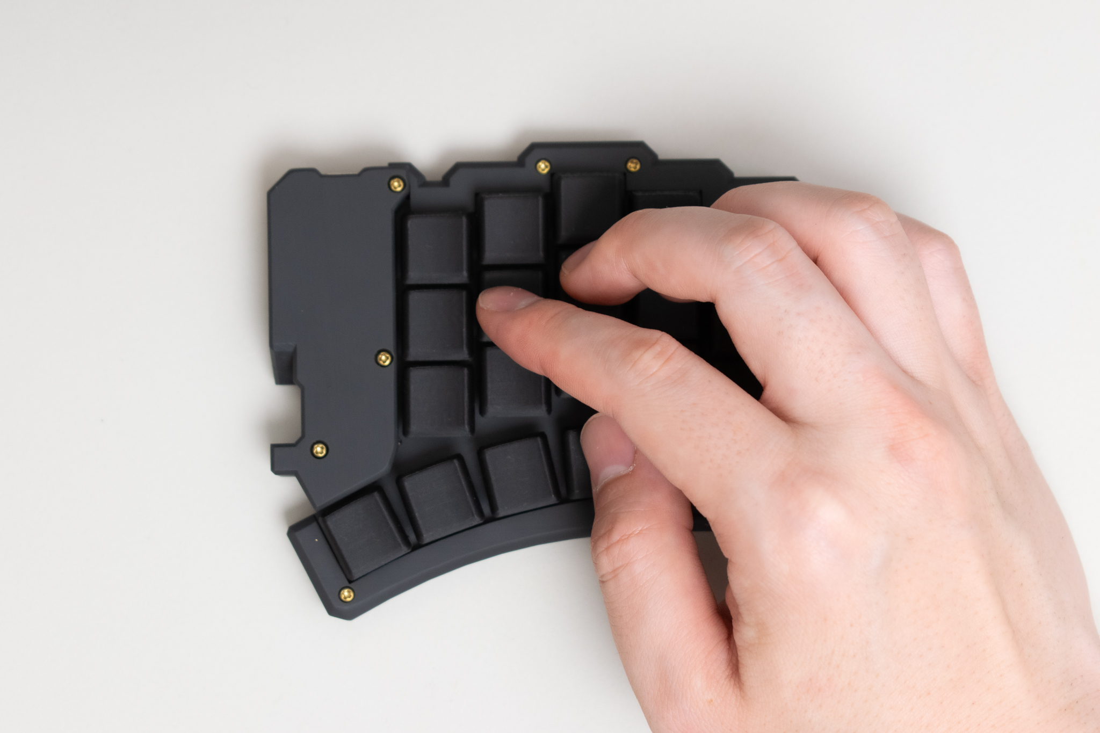
images/kinotsuyo/palmslave-54.jpg
