takashicompany/palmslave/images/kinotsuyo/palmslave-55.jpg

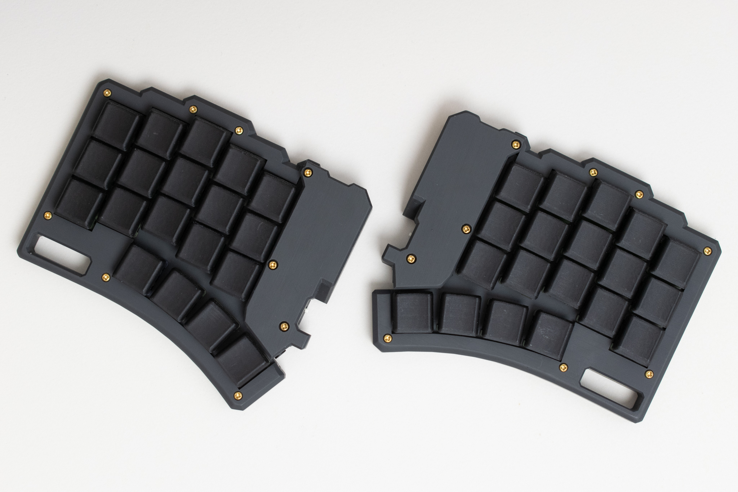
images/kinotsuyo/palmslave-55.jpg
