takashicompany/palmslave/images/kinotsuyo/palmslave-56.jpg

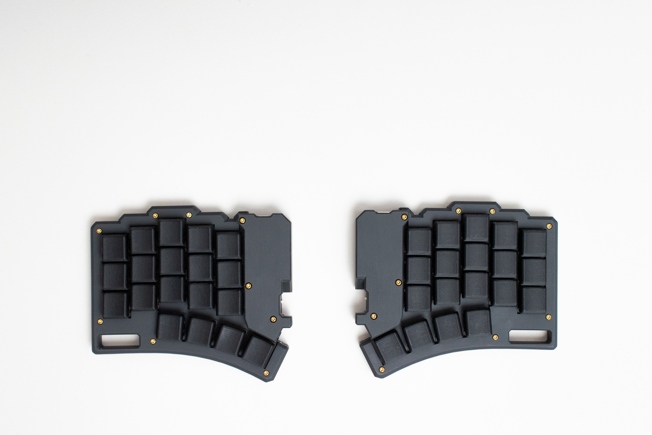
images/kinotsuyo/palmslave-56.jpg
