takashicompany/palmslave/images/kinotsuyo/palmslave-57.jpg

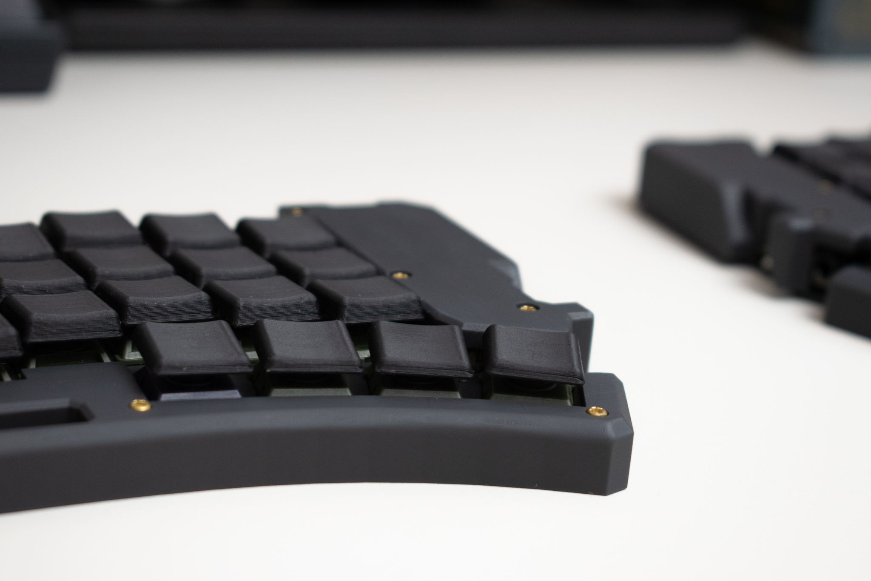
images/kinotsuyo/palmslave-57.jpg
