takashicompany/palmslave/images/kinotsuyo/palmslave-58.jpg

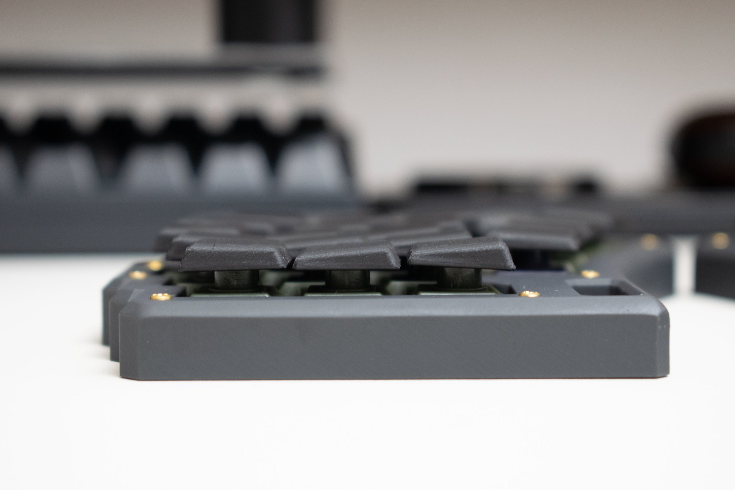
images/kinotsuyo/palmslave-58.jpg
