takashicompany/palmslave/case/3d-print/normal/top-plate_skirt-normal_right.stl

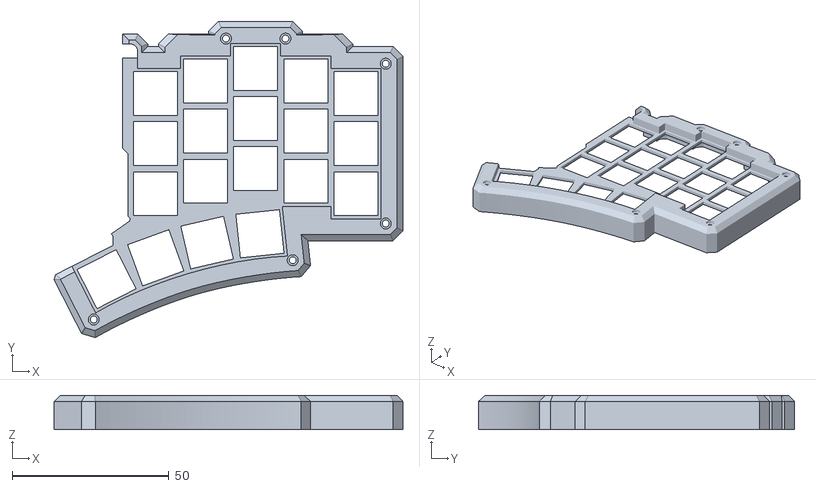
[picture p156: CAD file, 2025-04-18]
case/3d-print/normal/top-plate_skirt-normal_right.stl
111.3 x 100.9 x 11.0
