takashicompany/palmslave/images/build/IMG_0984.jpg

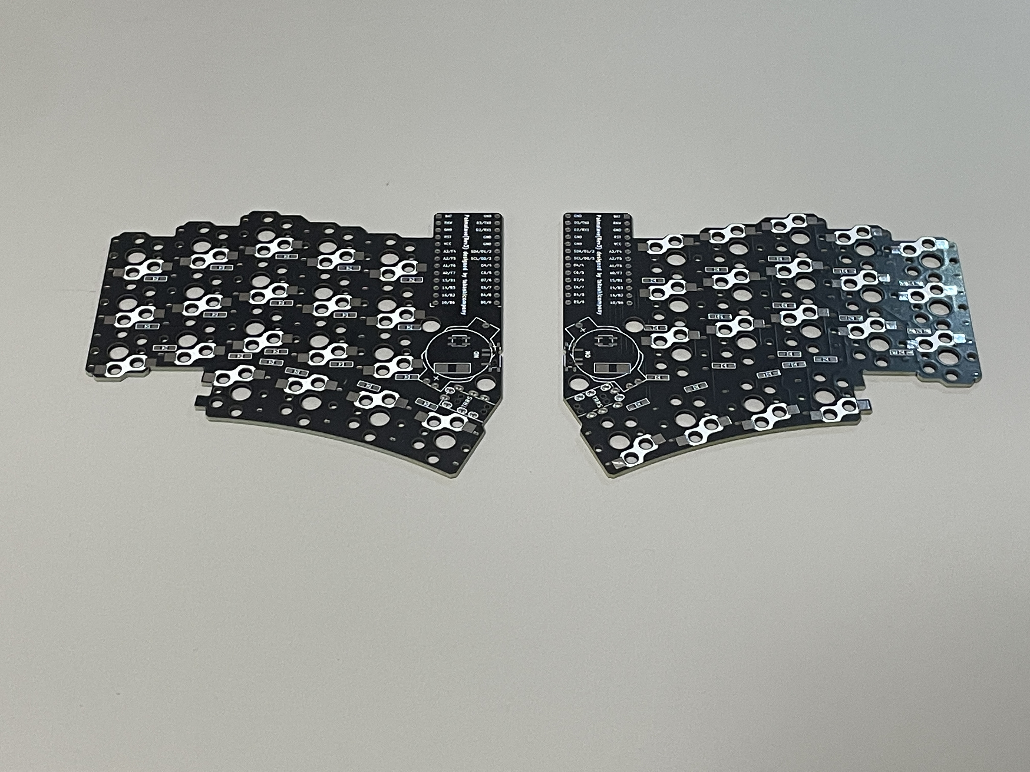
images/build/IMG_0984.jpg
