takashicompany/palmslave/images/build/IMG_0985.jpg

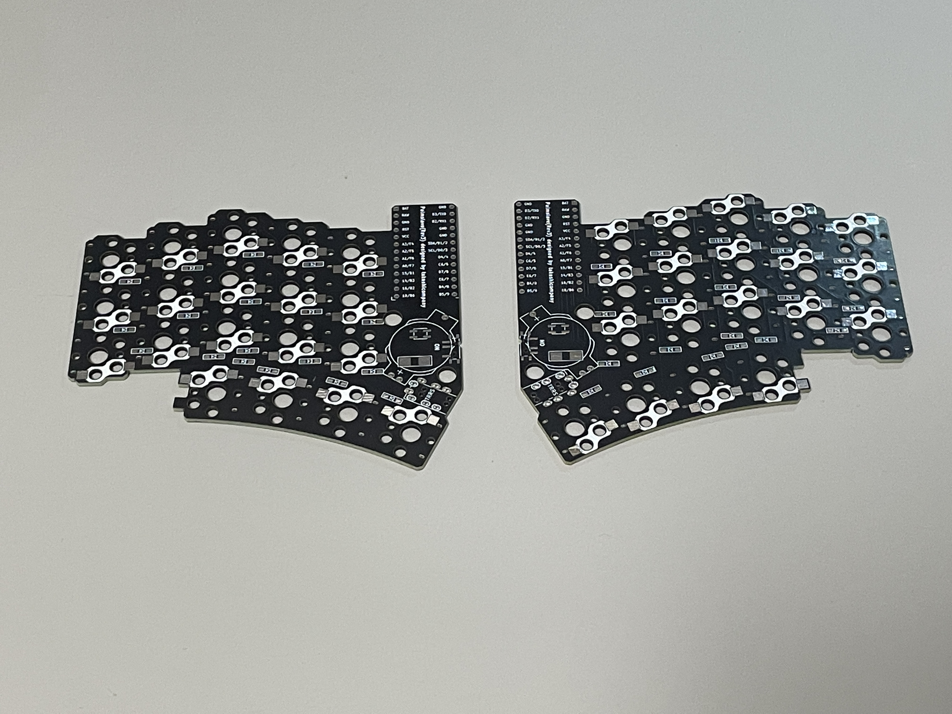
images/build/IMG_0985.jpg
