takashicompany/palmslave/images/build/IMG_0986.jpg

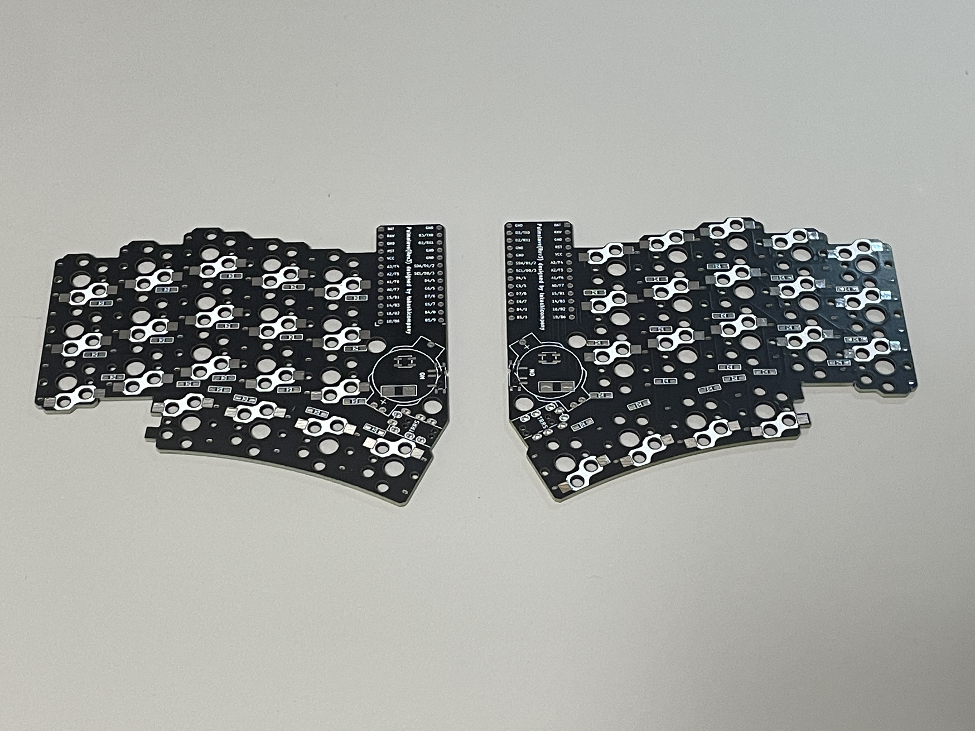
images/build/IMG_0986.jpg
