takashicompany/palmslave/images/build/IMG_0987.jpg

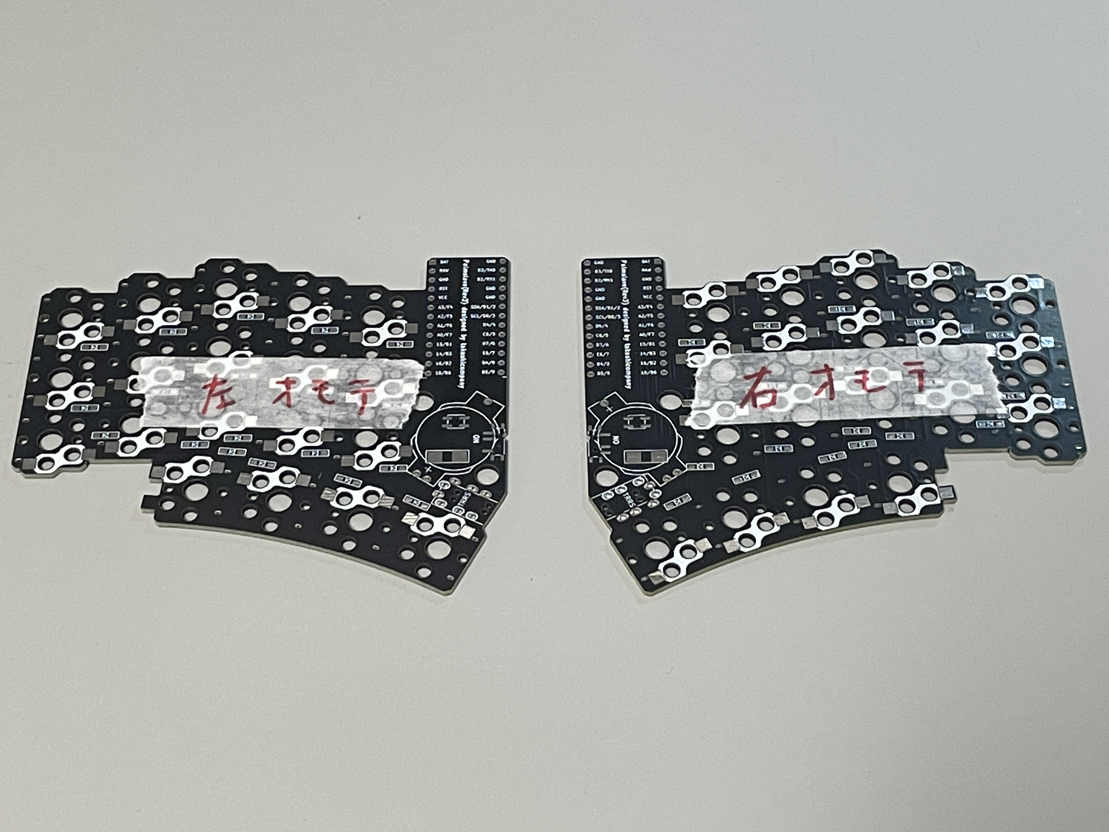
images/build/IMG_0987.jpg
