takashicompany/palmslave/images/build/IMG_0990.jpg

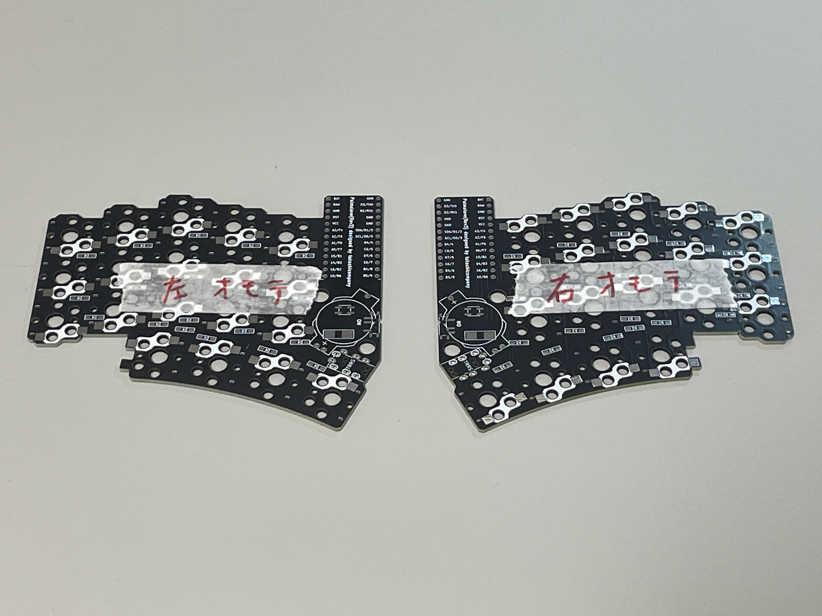
images/build/IMG_0990.jpg
