takashicompany/palmslave/images/build/IMG_0991.jpg

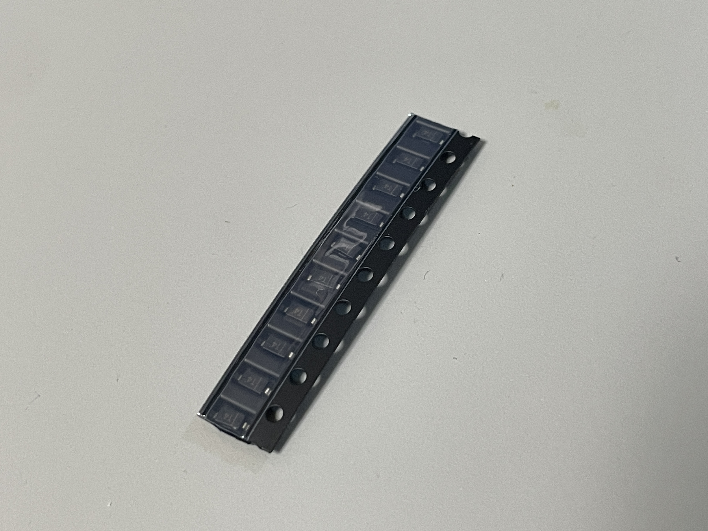
images/build/IMG_0991.jpg
