takashicompany/palmslave/images/build/IMG_0997.jpg

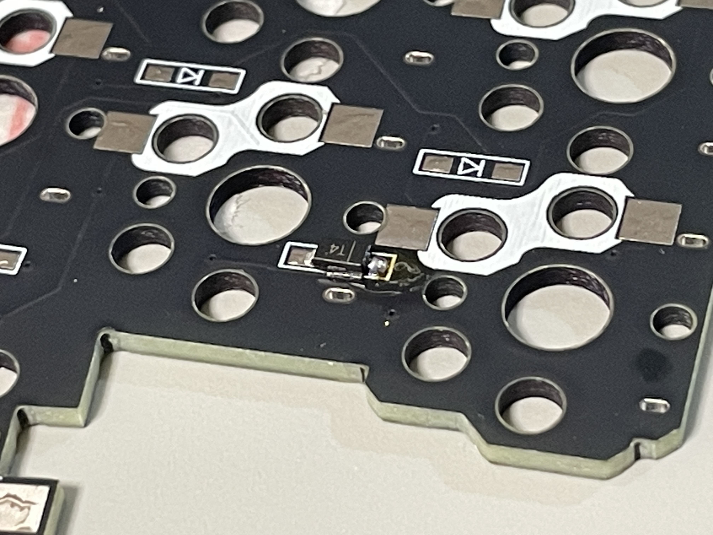
images/build/IMG_0997.jpg
