takashicompany/palmslave/images/build/IMG_1001.jpg

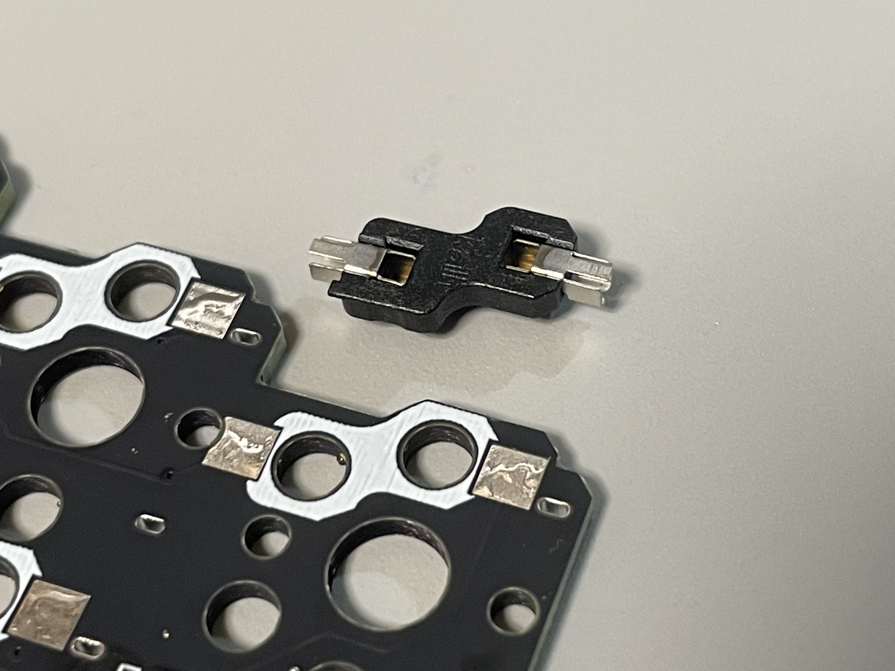
images/build/IMG_1001.jpg
