takashicompany/palmslave/images/build/IMG_1005.jpg

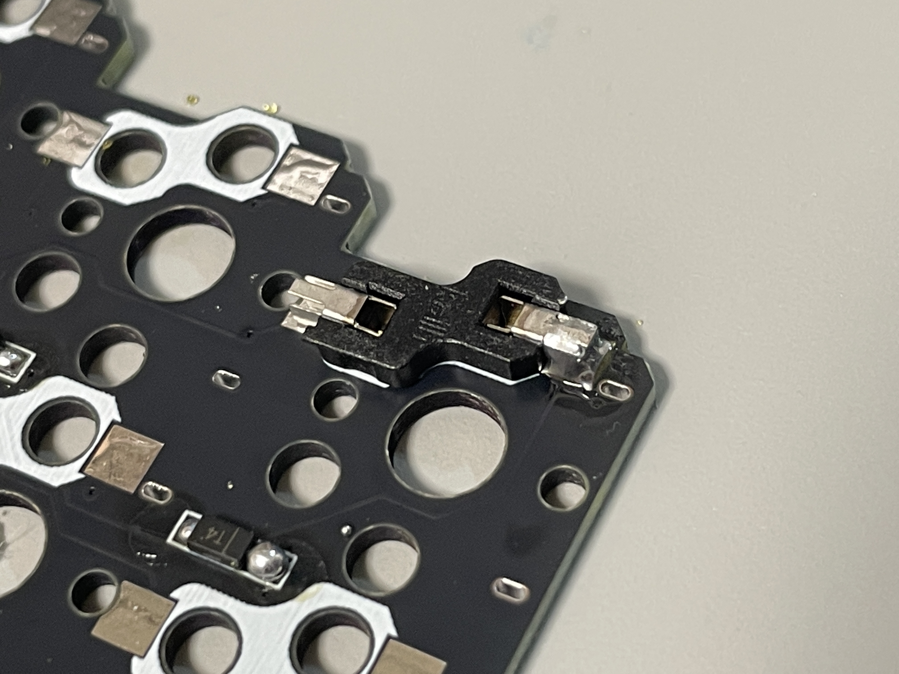
images/build/IMG_1005.jpg
