takashicompany/palmslave/images/build/IMG_1016.jpg

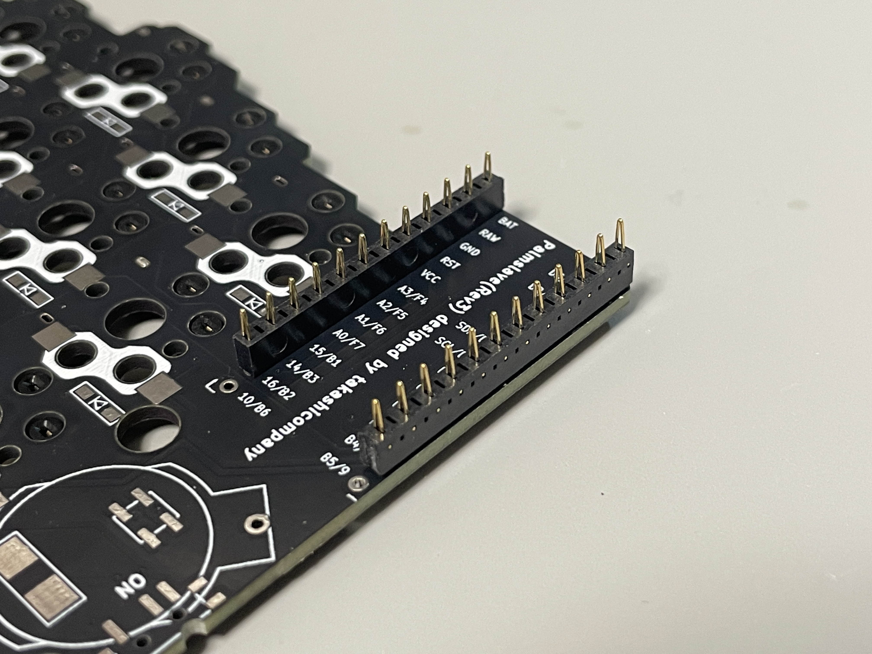
images/build/IMG_1016.jpg
