takashicompany/palmslave/images/build/IMG_1017.jpg

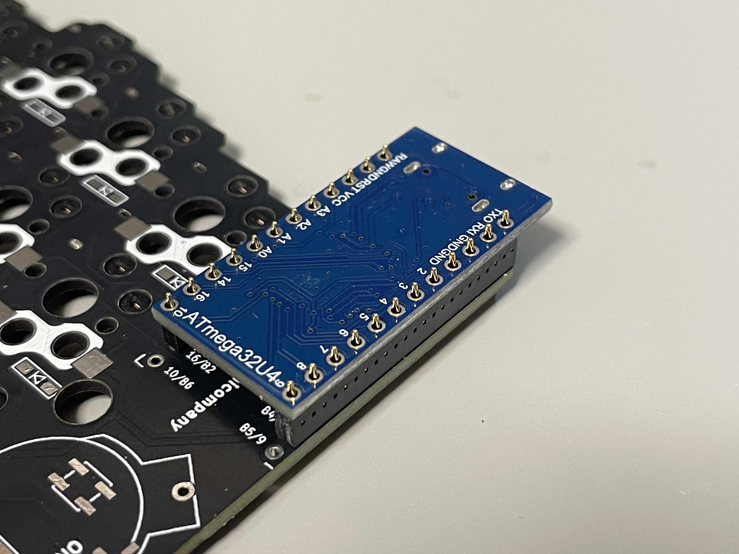
images/build/IMG_1017.jpg
