takashicompany/palmslave/images/build/IMG_1018.jpg

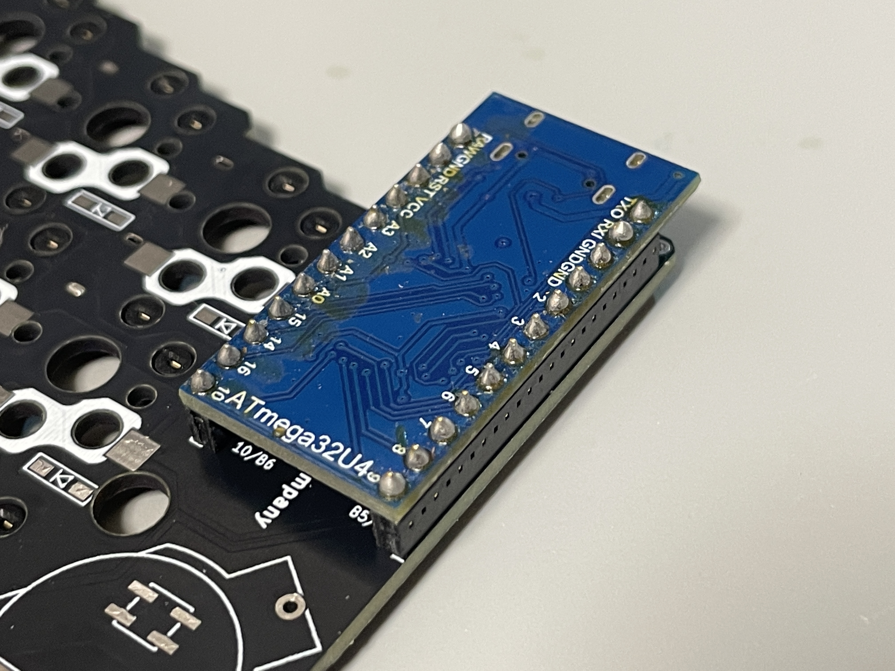
images/build/IMG_1018.jpg
