takashicompany/palmslave/images/build/IMG_1034.jpg

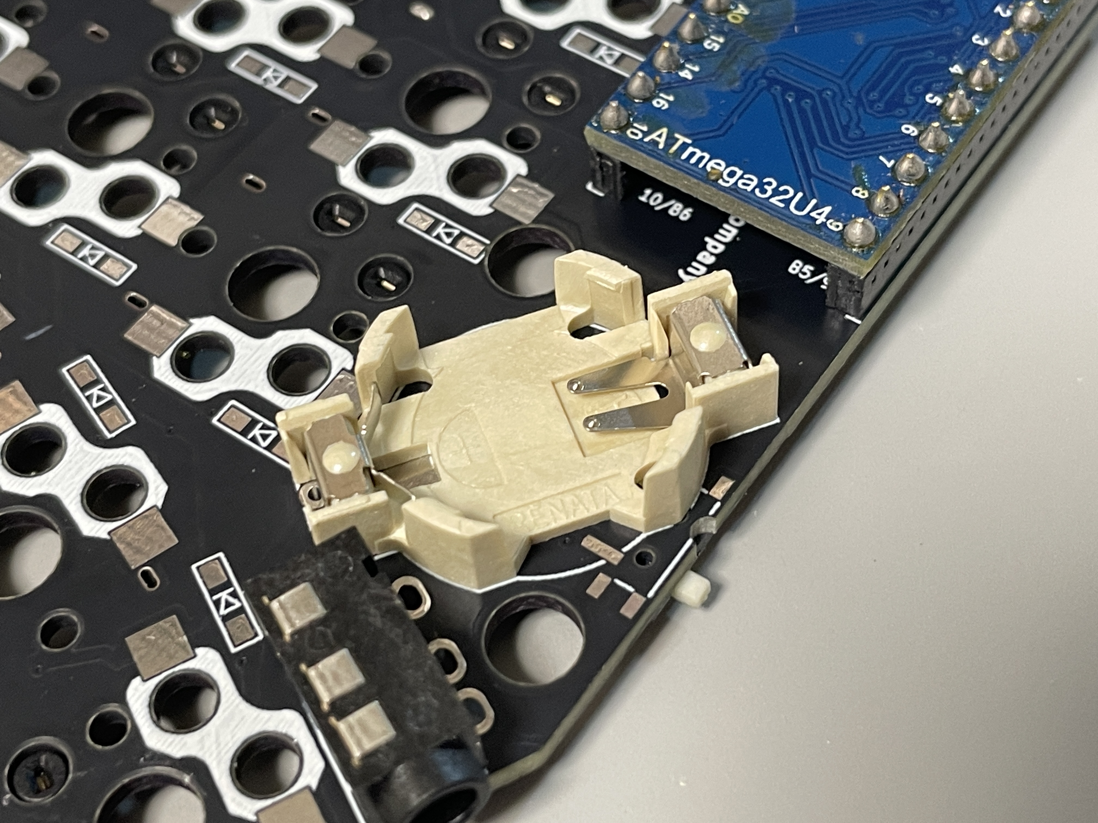
images/build/IMG_1034.jpg
