takashicompany/palmslave/images/build/IMG_1038.jpg

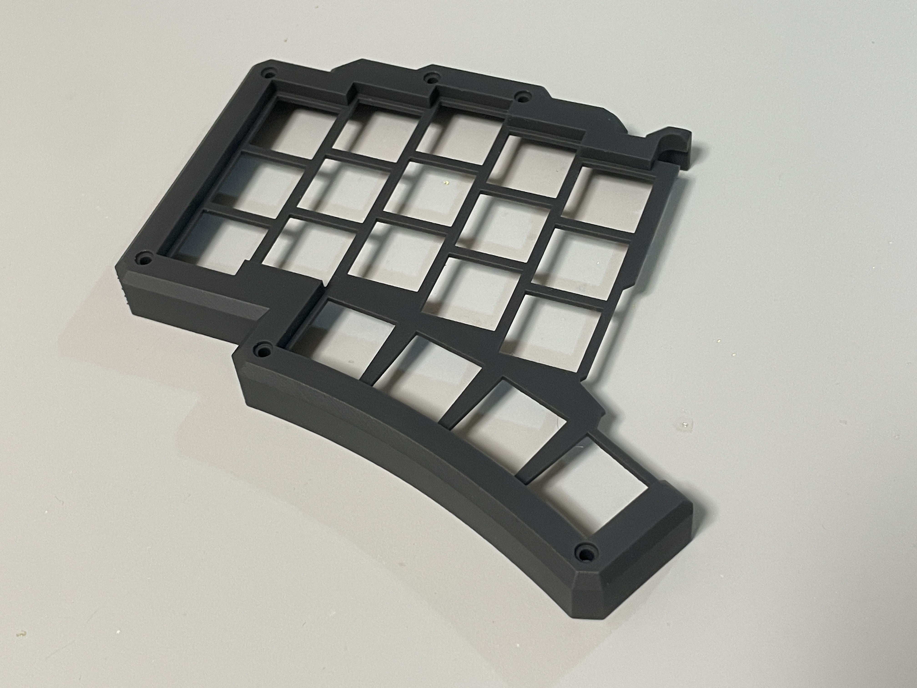
images/build/IMG_1038.jpg
