takashicompany/palmslave/images/build/IMG_1040.jpg

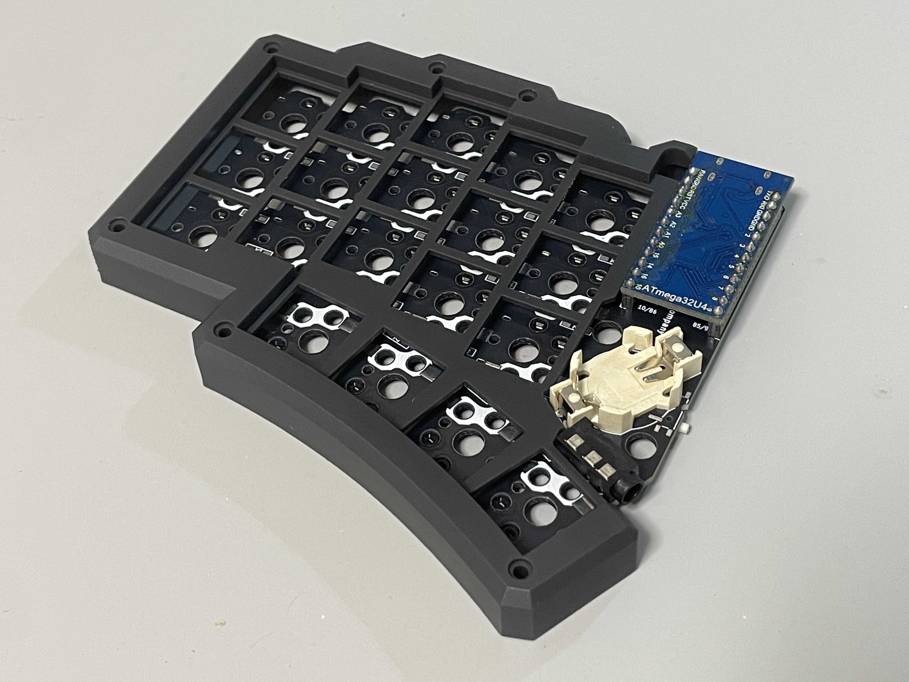
images/build/IMG_1040.jpg
