takashicompany/palmslave/images/build/IMG_1048.jpg

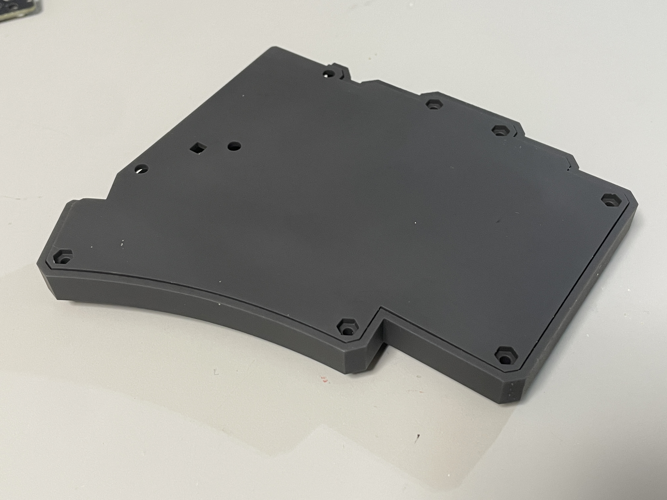
images/build/IMG_1048.jpg
