takashicompany/palmslave/images/build/IMG_1095.jpg

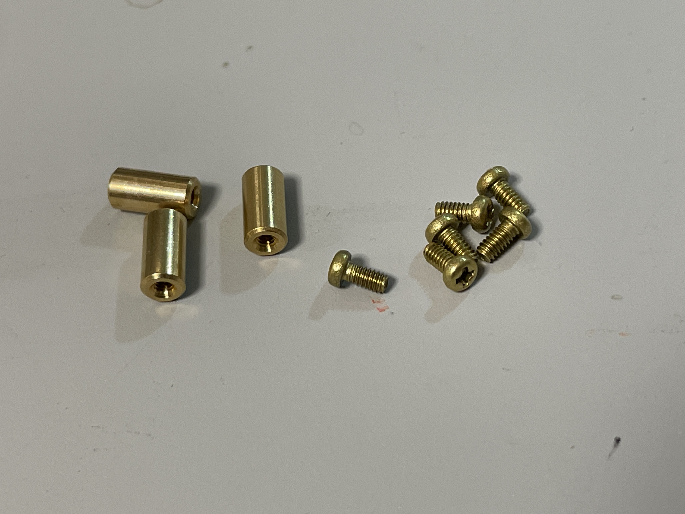
images/build/IMG_1095.jpg
