takashicompany/palmslave/images/build/IMG_1097.jpg

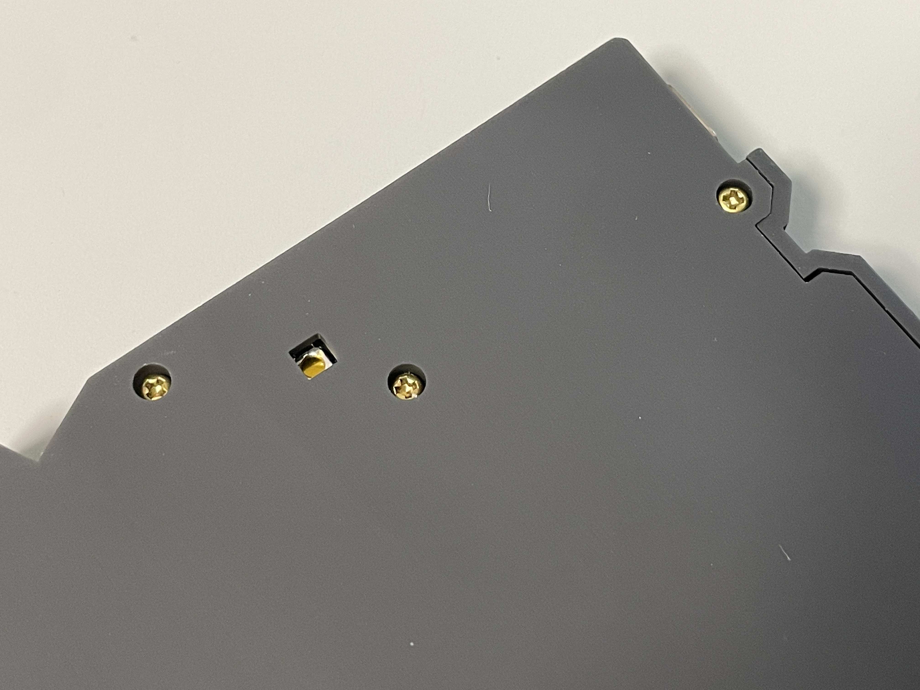
images/build/IMG_1097.jpg
