takashicompany/palmslave/images/build/IMG_1102.jpg

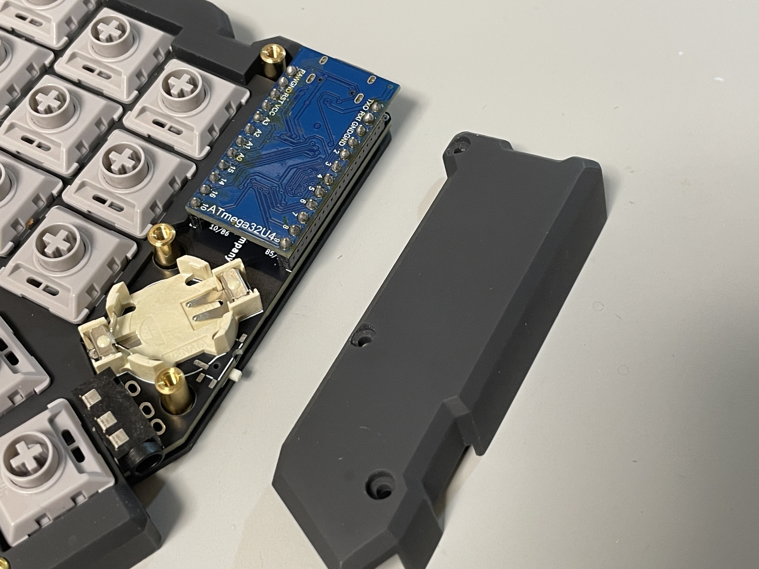
images/build/IMG_1102.jpg
