takashicompany/palmslave/images/build/IMG_1103.jpg

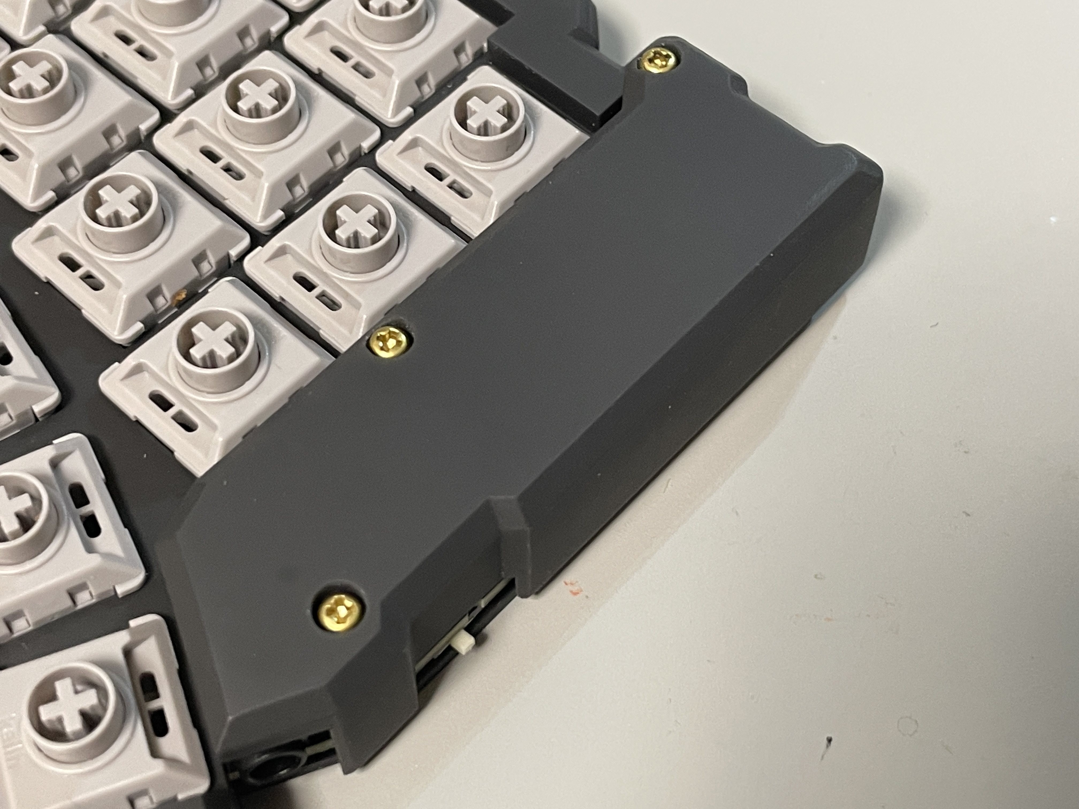
images/build/IMG_1103.jpg
