takashicompany/palmslave/images/build/IMG_1753.jpg

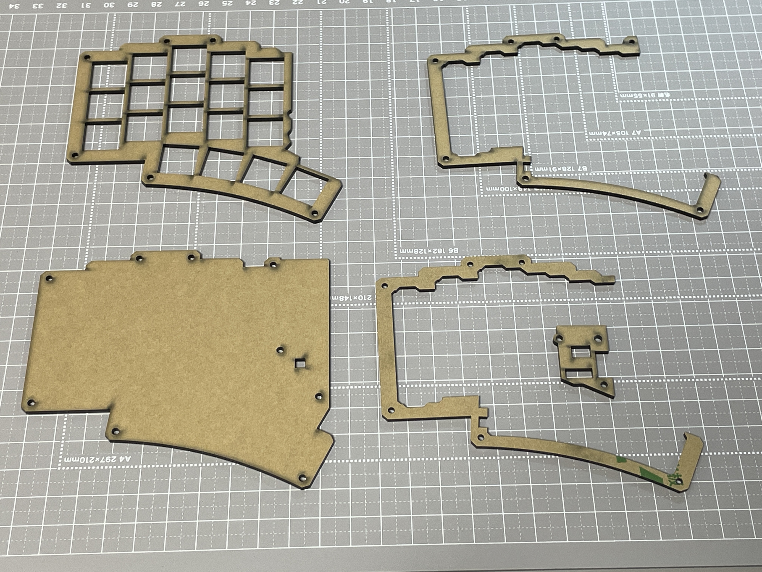
images/build/IMG_1753.jpg
