takashicompany/palmslave/images/build/IMG_1755.jpg

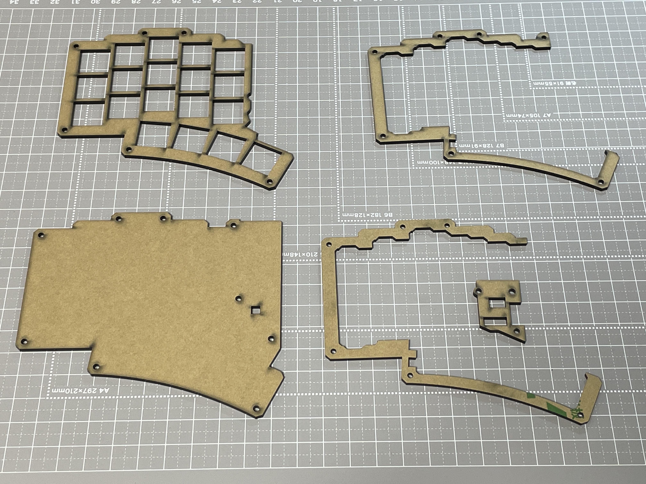
images/build/IMG_1755.jpg
