takashicompany/palmslave/images/build/IMG_1756.jpg

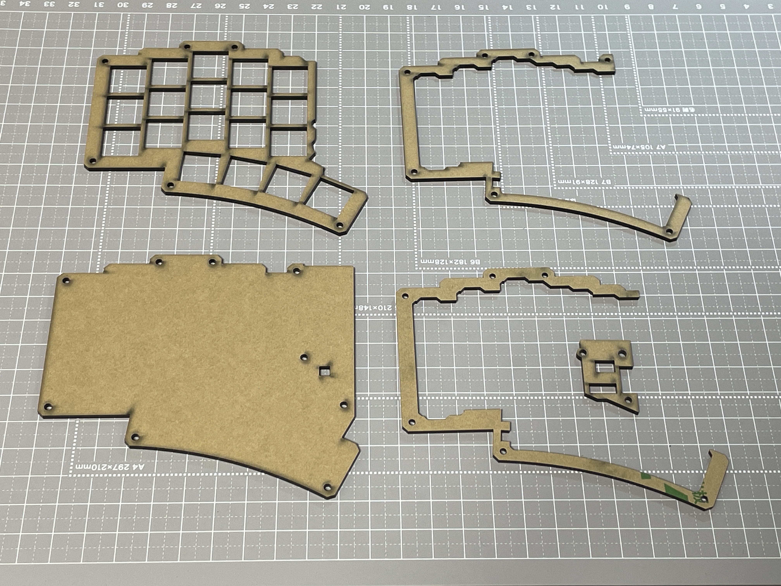
images/build/IMG_1756.jpg
