takashicompany/palmslave/images/build/IMG_1758.jpg

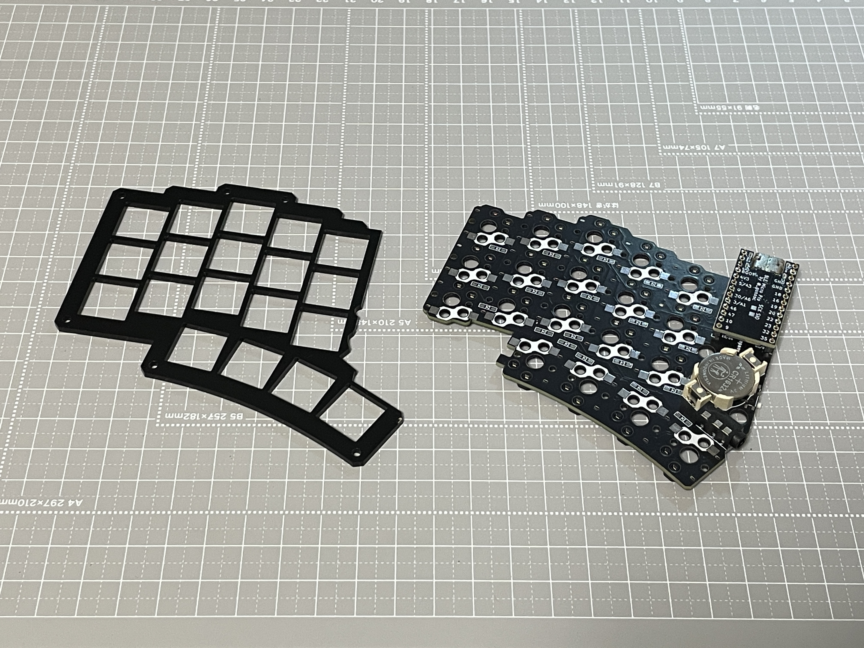
images/build/IMG_1758.jpg
