takashicompany/palmslave/images/build/IMG_1762.jpg

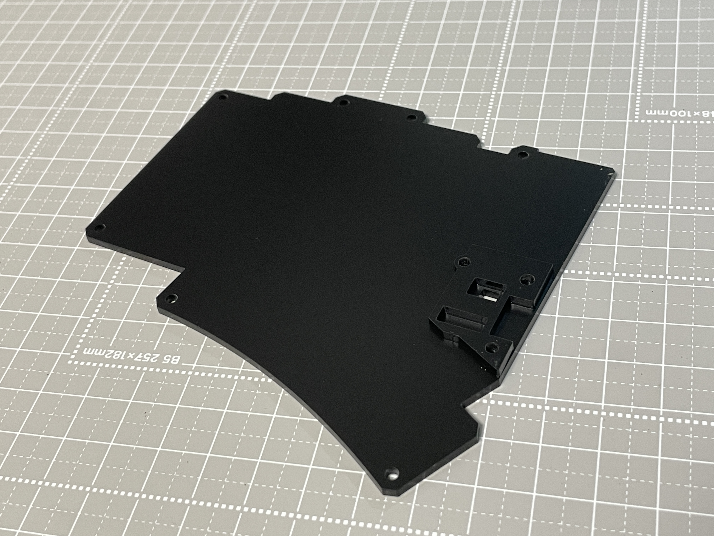
images/build/IMG_1762.jpg
