takashicompany/palmslave/images/build/IMG_1766.jpg

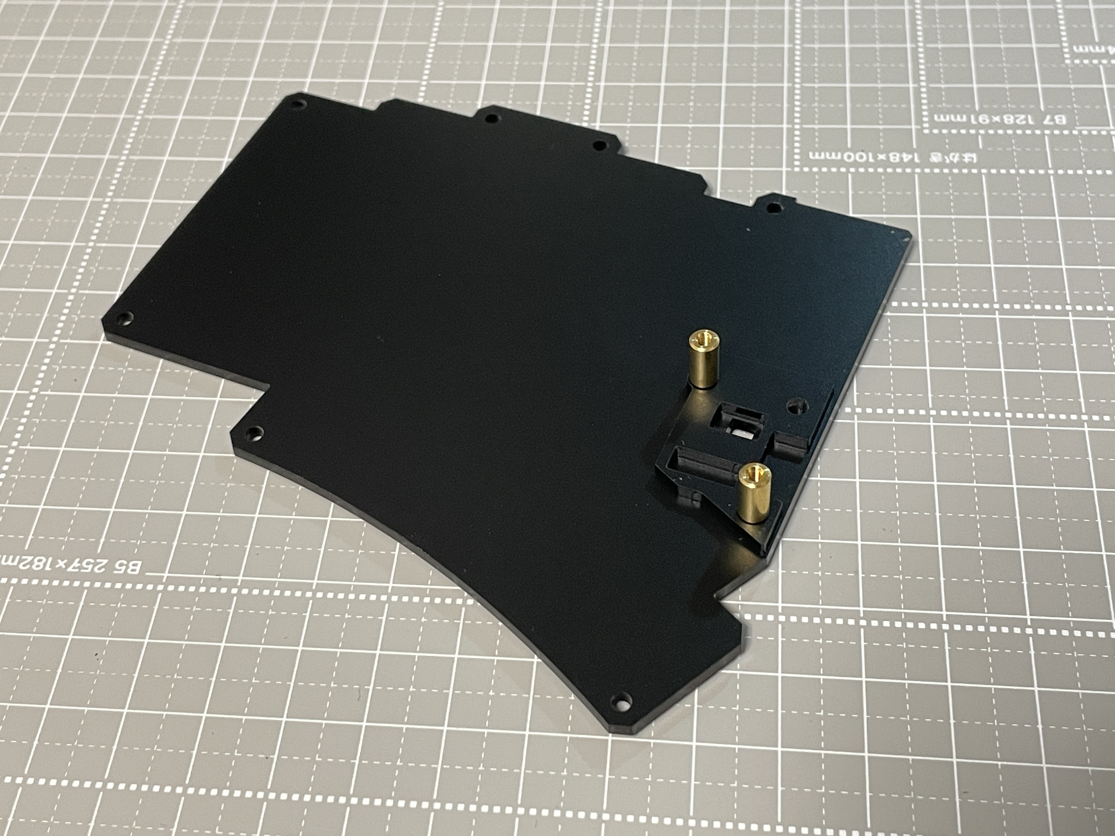
images/build/IMG_1766.jpg
