takashicompany/palmslave/images/build/IMG_2080.jpg

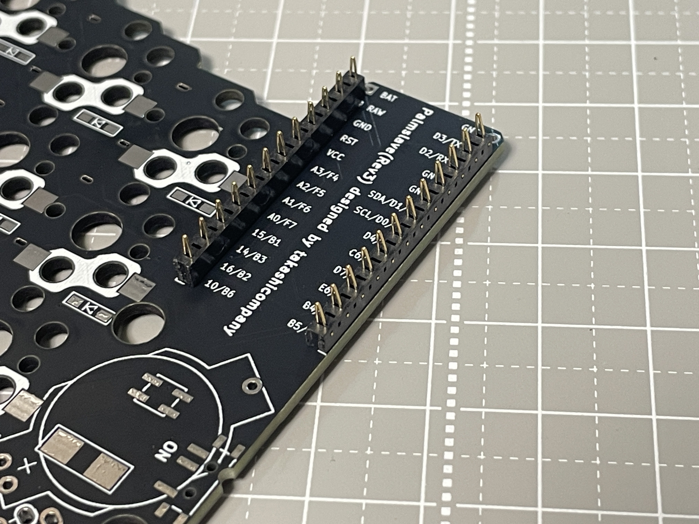
images/build/IMG_2080.jpg
