takashicompany/palmslave/images/build/IMG_2081.jpg

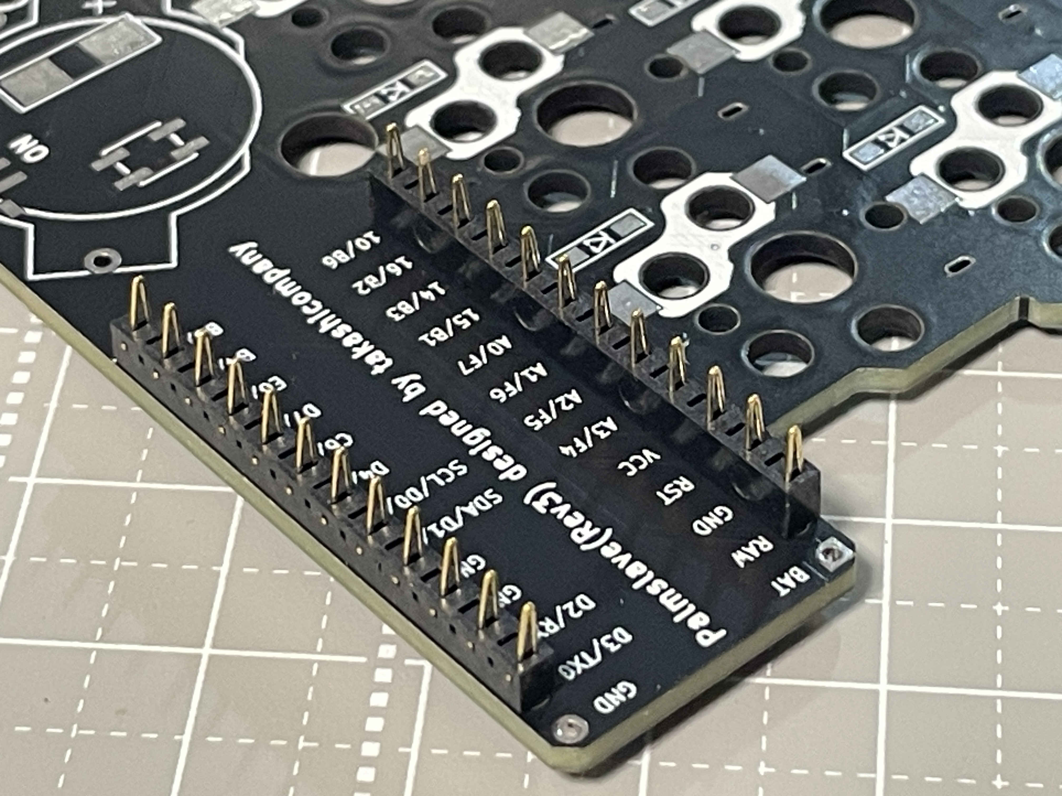
images/build/IMG_2081.jpg
