takashicompany/palmslave/images/build/IMG_2082.jpg

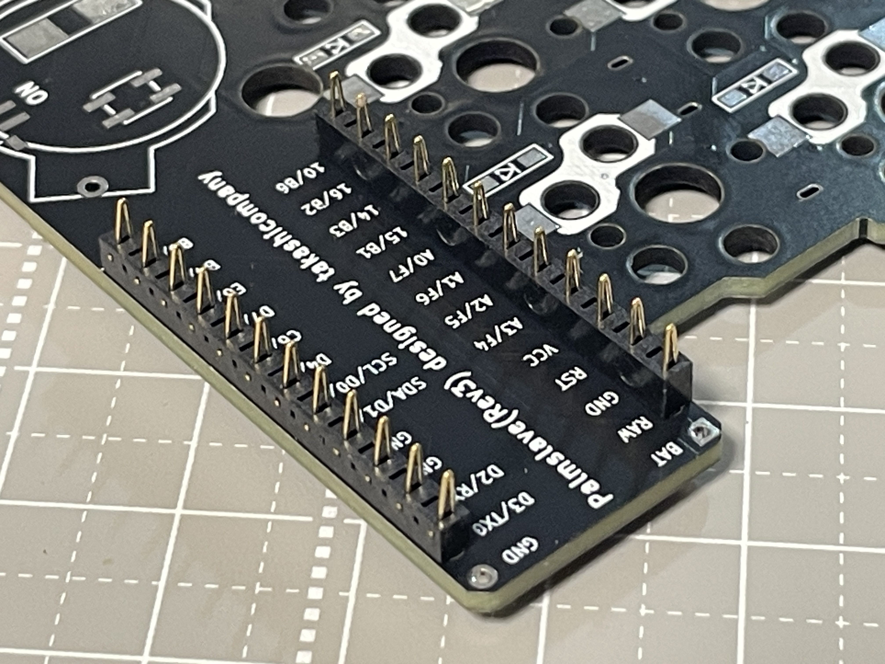
images/build/IMG_2082.jpg
