takashicompany/palmslave/images/build/IMG_2084.jpg

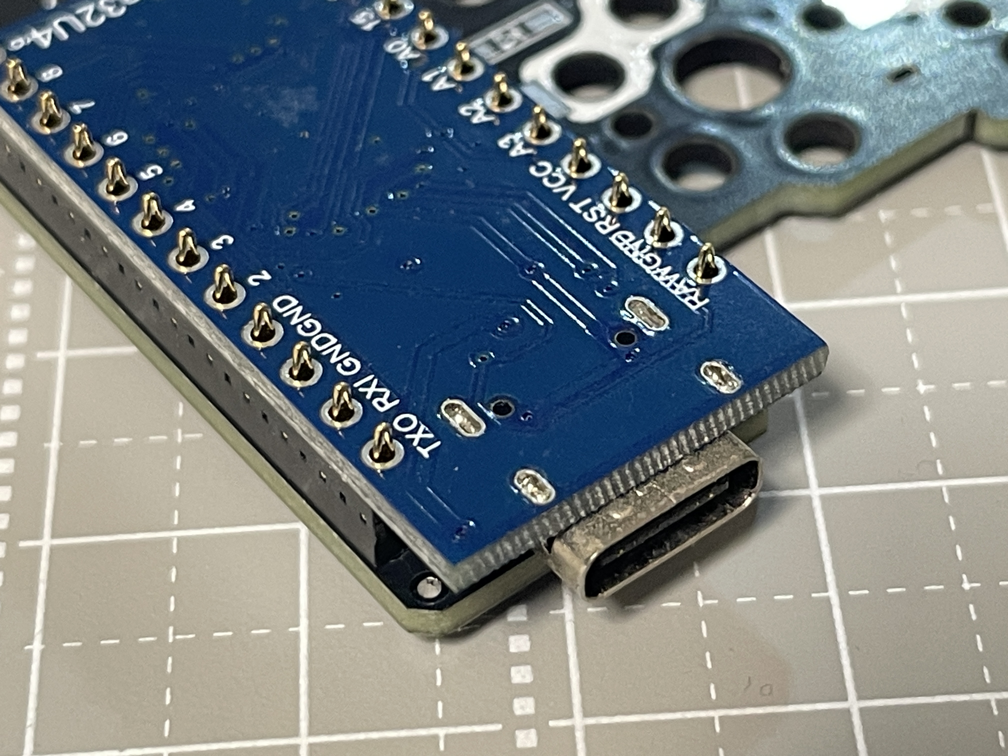
images/build/IMG_2084.jpg
