takashicompany/palmslave/images/build/IMG_2086.jpg

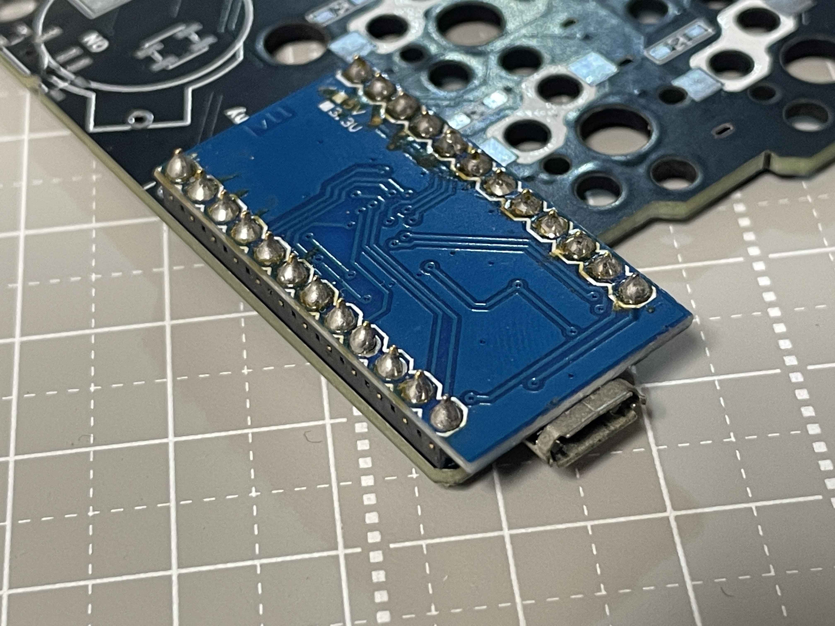
images/build/IMG_2086.jpg
