takashicompany/palmslave/images/build/IMG_2089.jpg

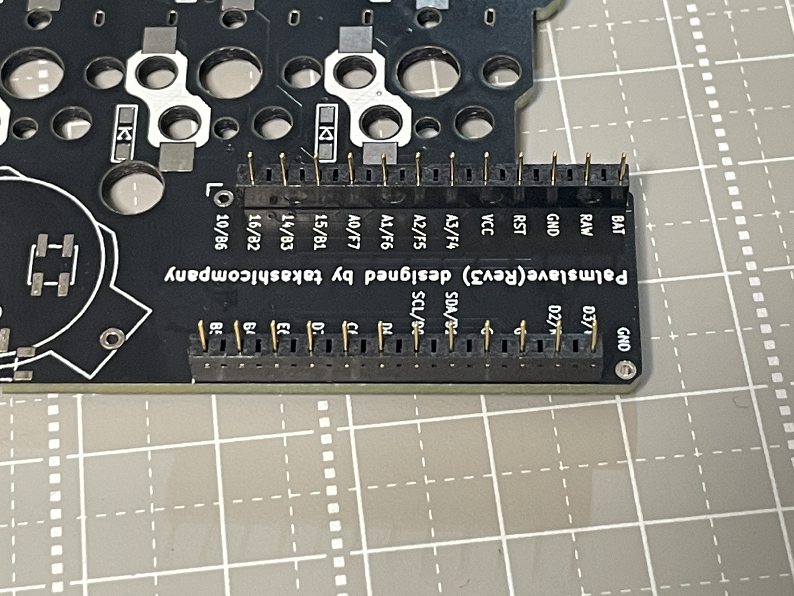
images/build/IMG_2089.jpg
