takashicompany/palmslave/images/build/IMG_2090.jpg

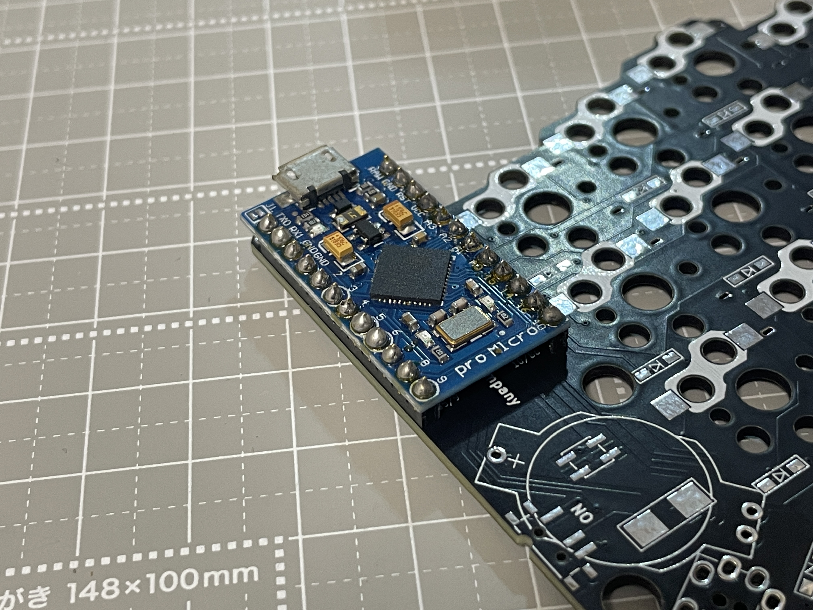
images/build/IMG_2090.jpg
